dczia/thirtyinone/Hardware/badge/images/build-instructions.pdf

# Hamster’s Build Instructions

## You will need

Wire Cutters
Soldering Iron
Rosin Core Solder

Locate the 5 long socket strips. They look like this:

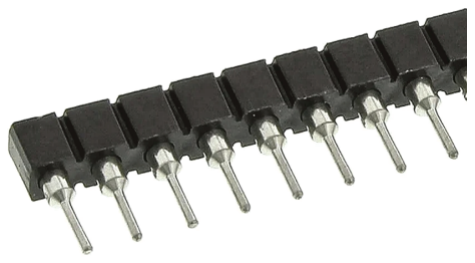
[picture p8: figure]

Using your wire cutters or your fingers, snap off 2-pin

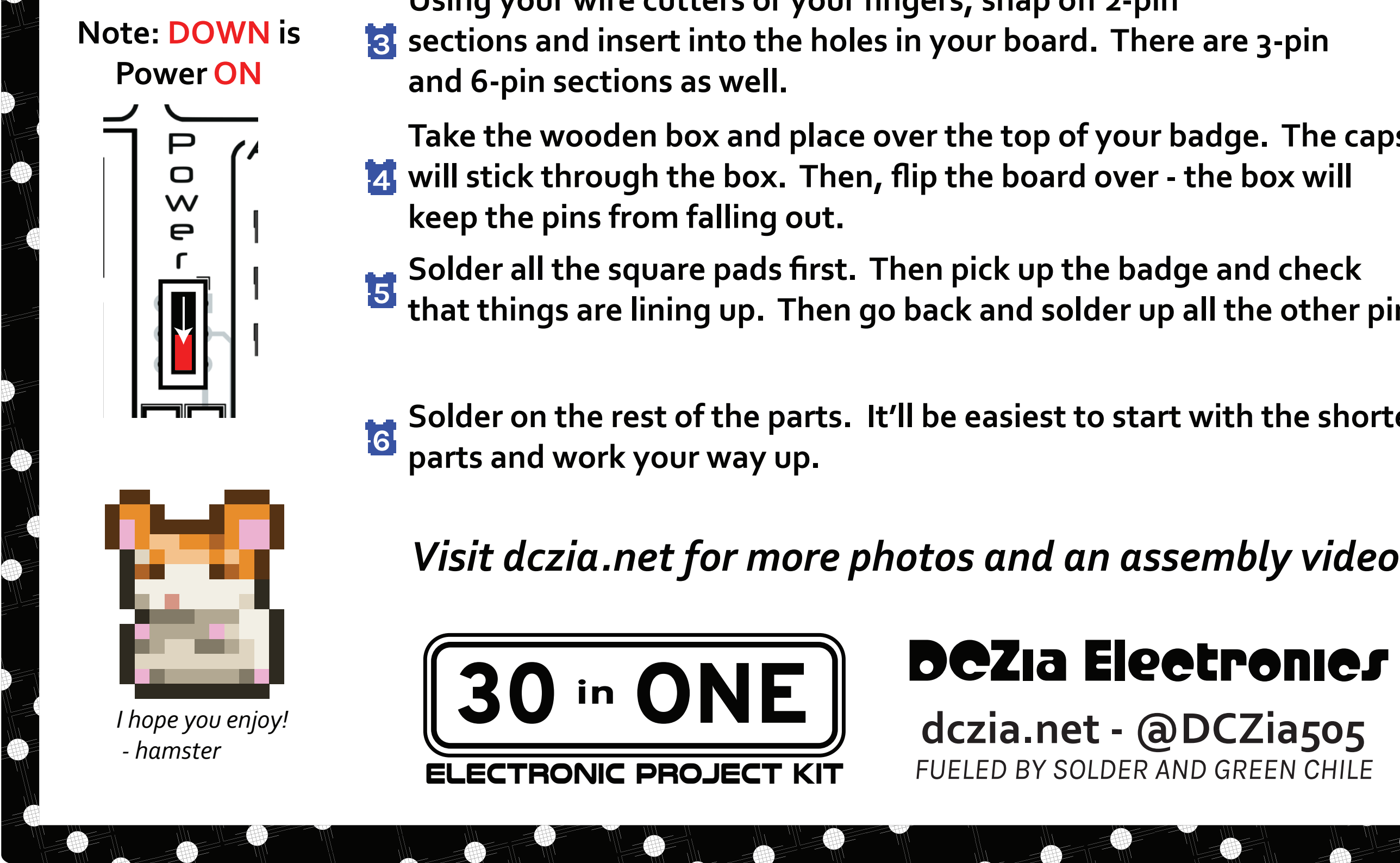
[picture p9: figure]
DCZia Electronics 30; ELECTRONIC PROJECT KIT; in ONE; and 6-pin sections as well.; keep the pins from falling out.; parts and work your way up.; Note: DOWN is Power ON; I hope you enjoy!; - hamster; dczia.net - @DCZia505; FUELED BY SOLDER AND GREEN CHILE

sections and insert into the holes in your board. There are 3-pin

Take the wooden box and place over the top of your badge. The caps will stick through the box. Then, flip the board over - the box will

Solder all the square pads first. Then pick up the badge and check that things are lining up. Then go back and solder up all the other pins.

Solder on the rest of the parts. It’ll be easiest to start with the shortest

Remove the top of the box and pull out your board and place it face up on the table.

## Visit dczia.net for more photos and an assembly video

1

2
