dczia/thirtyinone/Hardware/badge/outputs/thirtyinone-badge.pdf

File: thirtyinone-badge.kicad_sch Sheet: / DCZia

Id: 1/2 Title: 30-in-One


defcon 30
Sheet: /Analog Circuits/ DCZia

File: circuits.kicad_sch
Id: 2/2 Title: 30-in-One
