dczia/thirtyinone/Hardware/circuits/outputs/thirtyinone-circuits.pdf

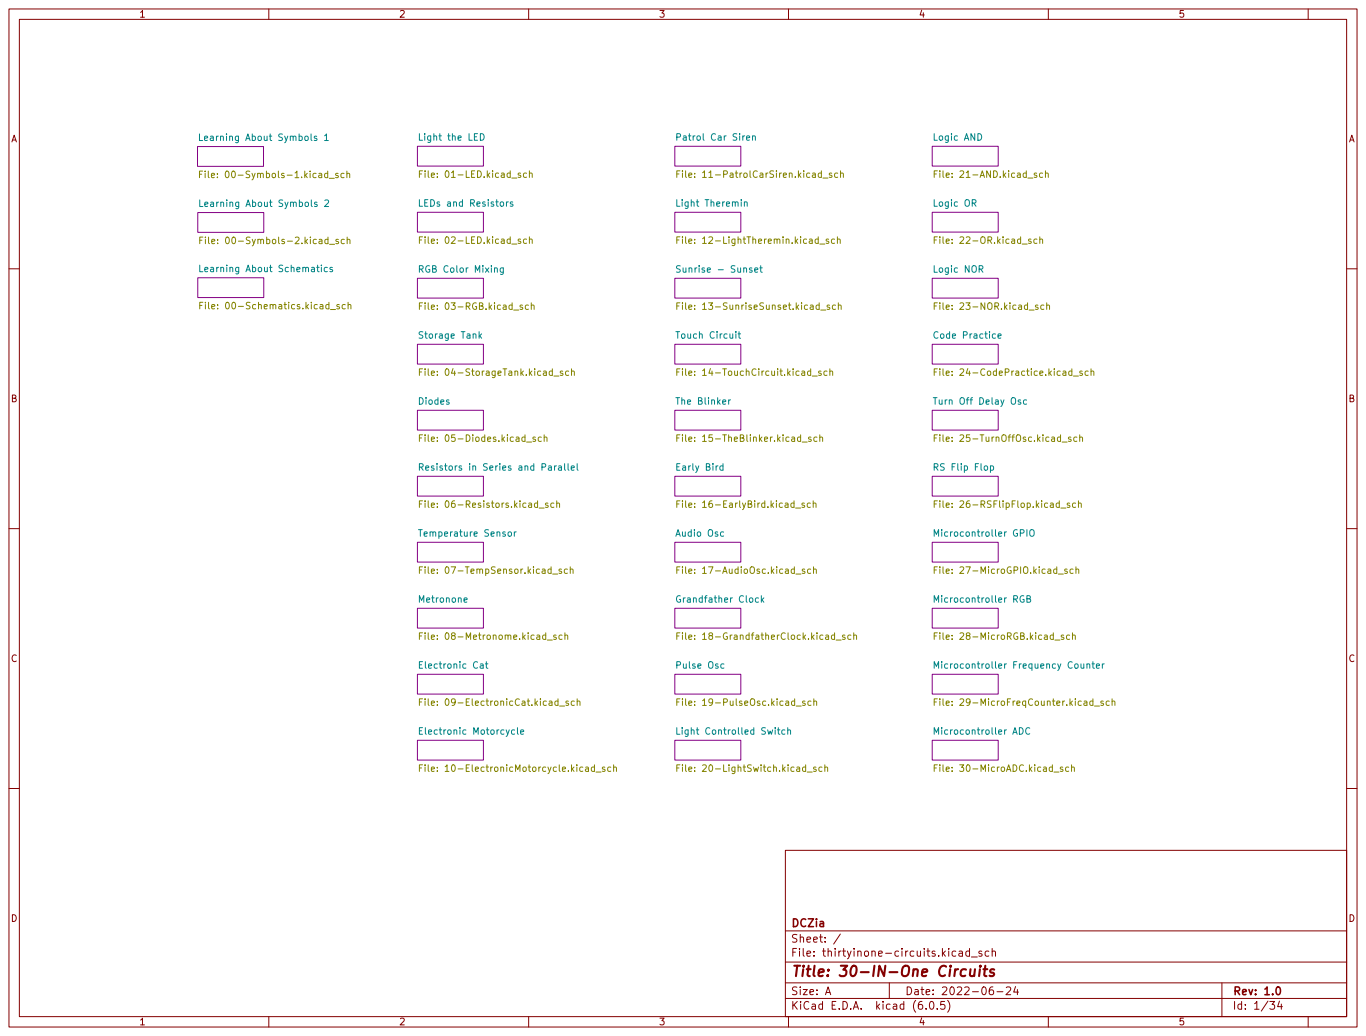
[picture p24: page 1]

File: 16-EarlyBird.kicad_sch Sunrise - Sunset File: 13-SunriseSunset.kicad_sch The Blinker File: 15-TheBlinker.kicad_sch Touch Circuit File: 14-TouchCircuit.kicad_sch Patrol Car Siren File: 11-PatrolCarSiren.kicad_sch
File: 21-AND.kicad_sch Turn Off Delay Osc File: 25-TurnOffOsc.kicad_sch

LEDs and Resistors File: 02-LED.kicad_sch

Learning About Schematics File: 00-Schematics.kicad_sch

Diodes File: 05-Diodes.kicad_sch Temperature Sensor

File: 20-LightSwitch.kicad_sch Grandfather Clock File: 18-GrandfatherClock.kicad_sch Early Bird

File: 26-RSFlipFlop.kicad_sch Microcontroller GPIO

File: 27-MicroGPIO.kicad_sch Microcontroller Frequency Counter

File: 30-MicroADC.kicad_sch Microcontroller RGB

File: 29-MicroFreqCounter.kicad_sch Microcontroller ADC

File: thirtyinone-circuits.kicad_sch Sheet: / DCZia

Id: 1/34 Title: 30-IN-One Circuits

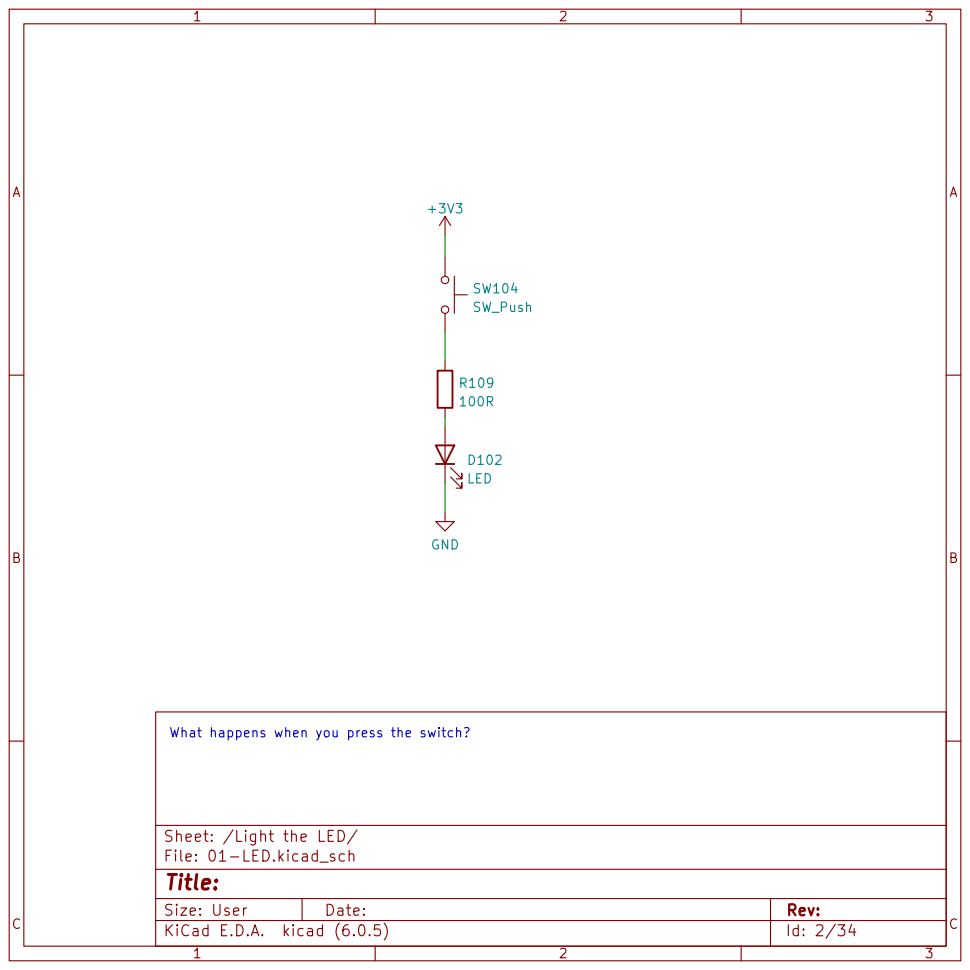
[picture p25: page 2]

LED GND What happens when you press the switch?

Sheet: /Light the LED/
File: 01-LED.kicad_sch
Id: 2/34 Title:

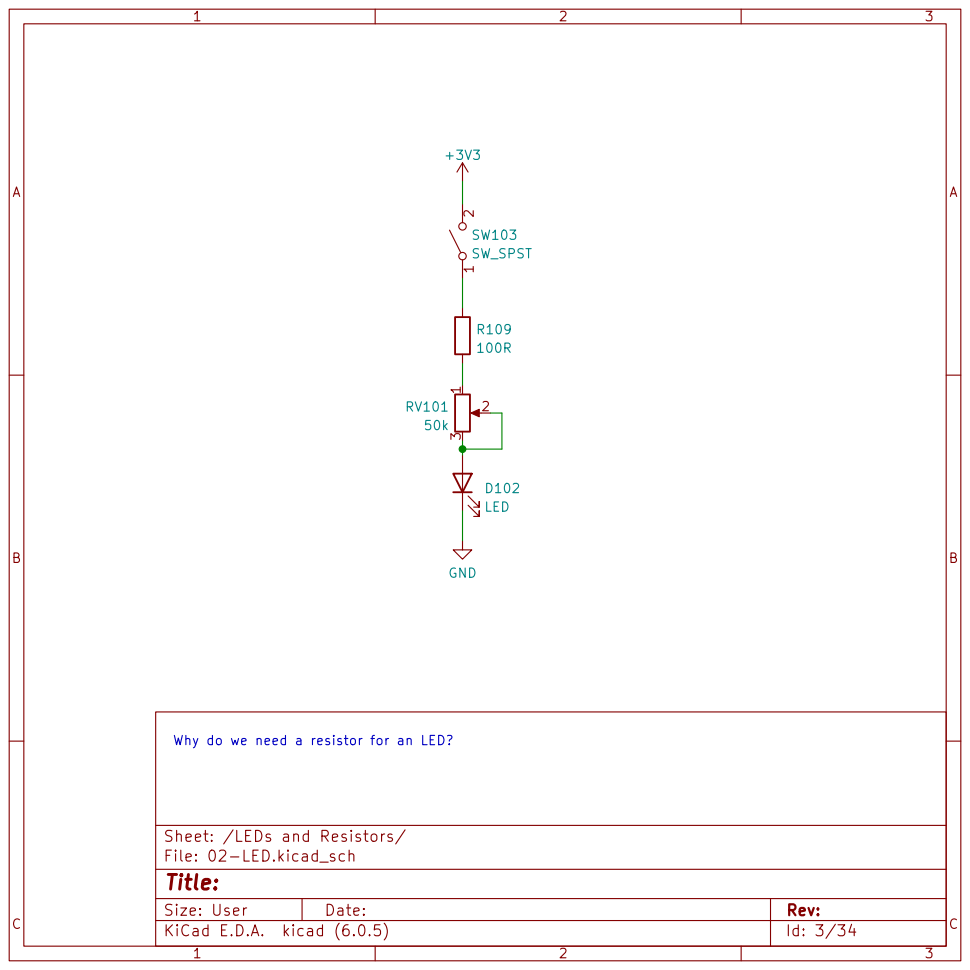
[picture p26: page 3]

1 2 SW103 SW_SPST Why do we need a resistor for an LED?

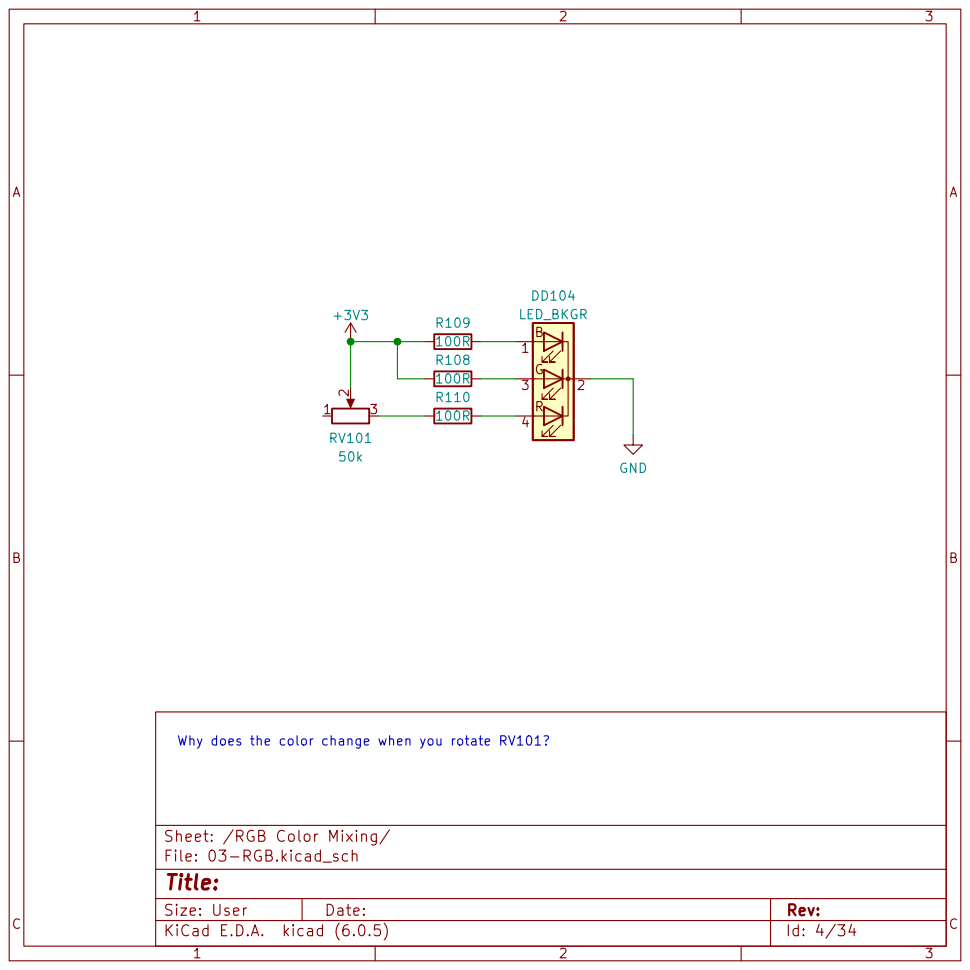
[picture p27: page 4]

50k Why does the color change when you rotate RV101?

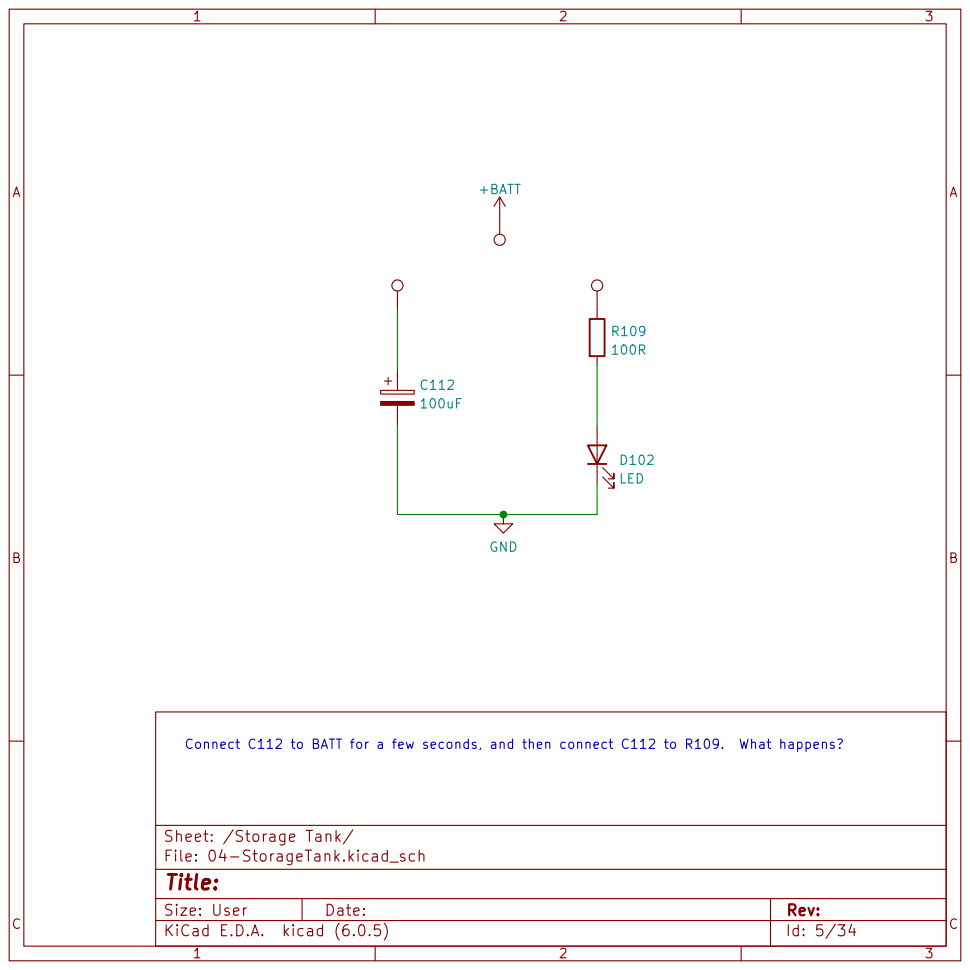
[picture p28: page 5]

+BATT Connect C112 to BATT for a few seconds, and then connect C112 to R109. What happens?

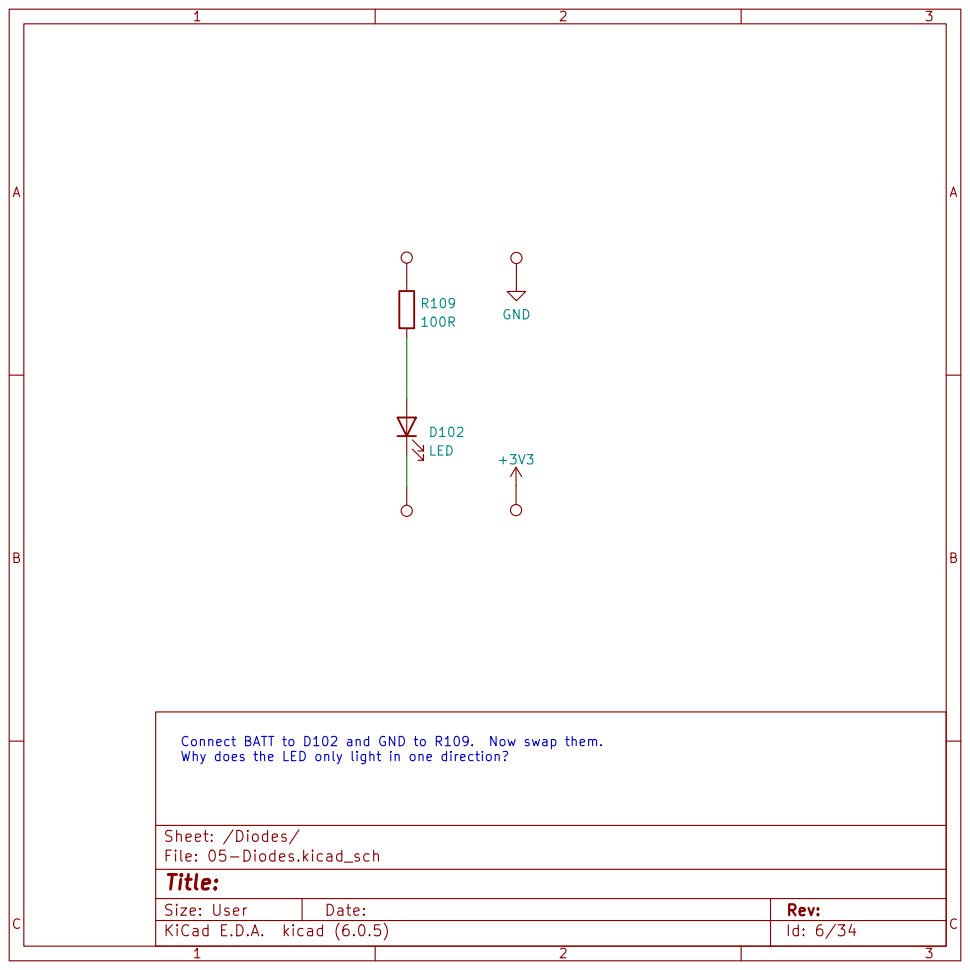
[picture p29: page 6]

+3V3 Connect BATT to D102 and GND to R109. Now swap them.

Why does the LED only light in one direction?

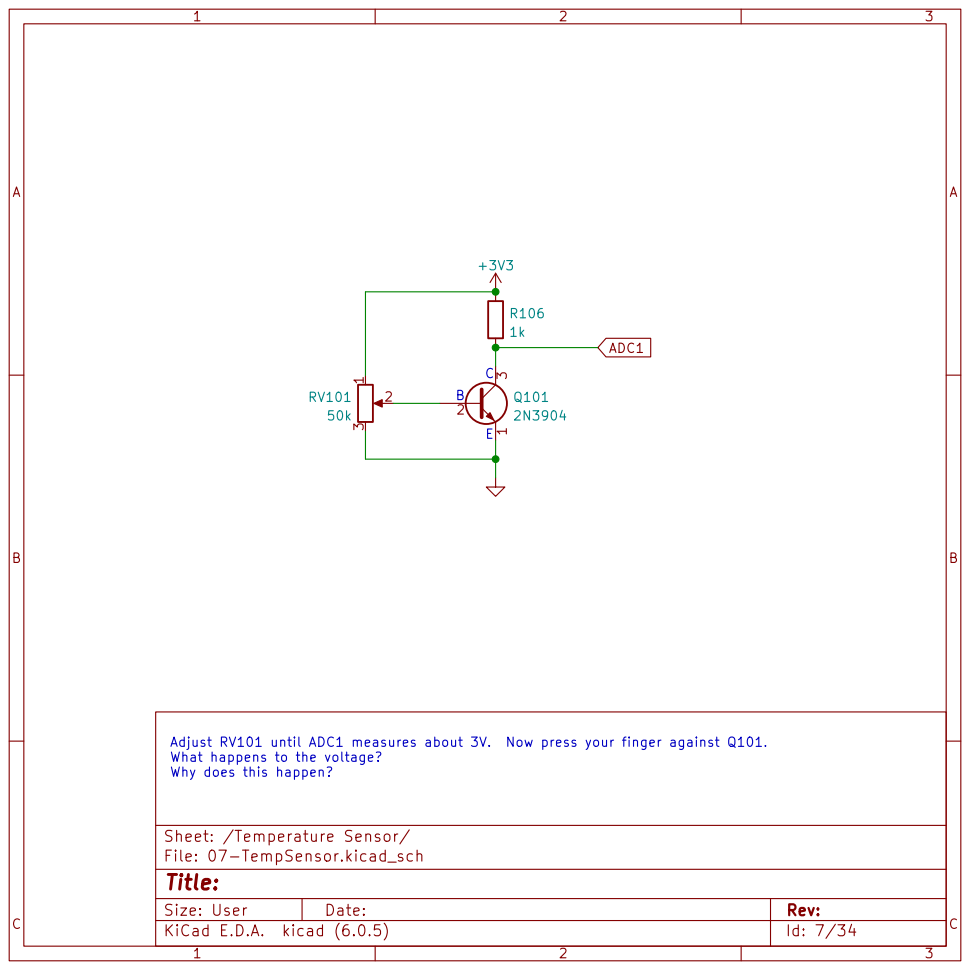
[picture p30: page 7]

Adjust RV101 until ADC1 measures about 3V. Now press your finger against Q101.
What happens to the voltage?
Why does this happen?

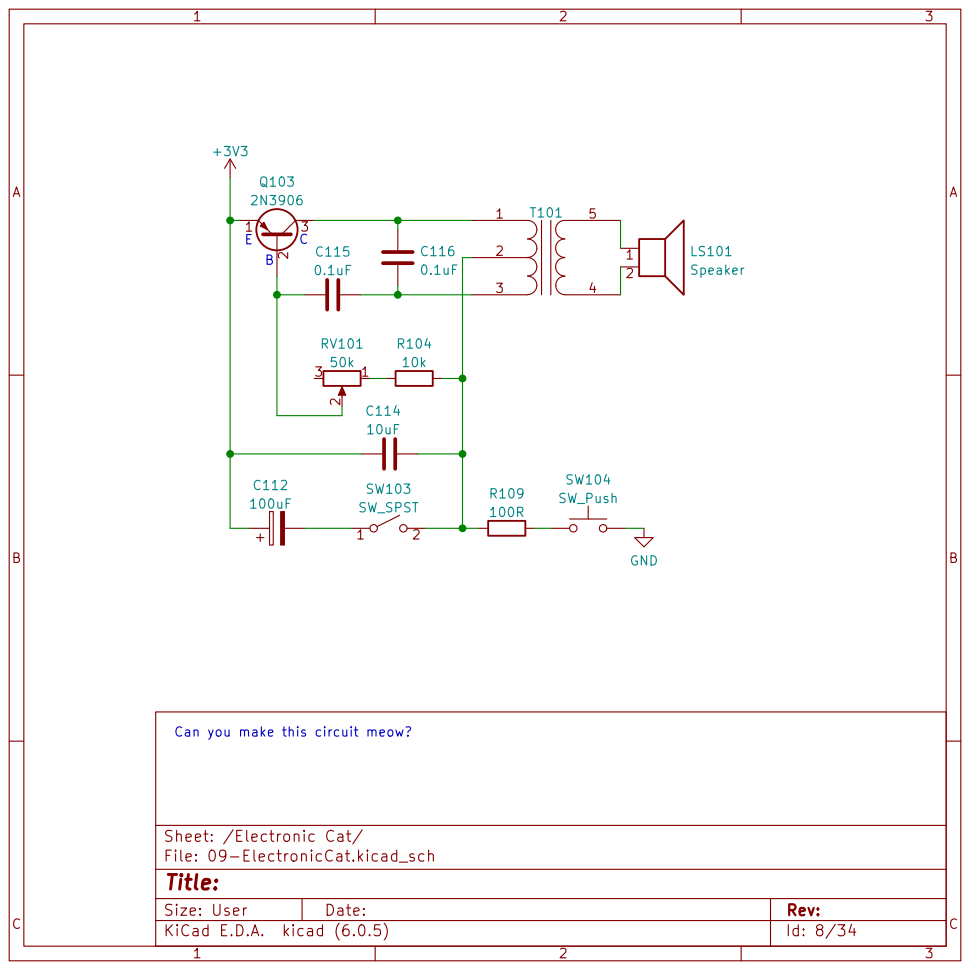
[picture p31: page 8]

Can you make this circuit meow? B

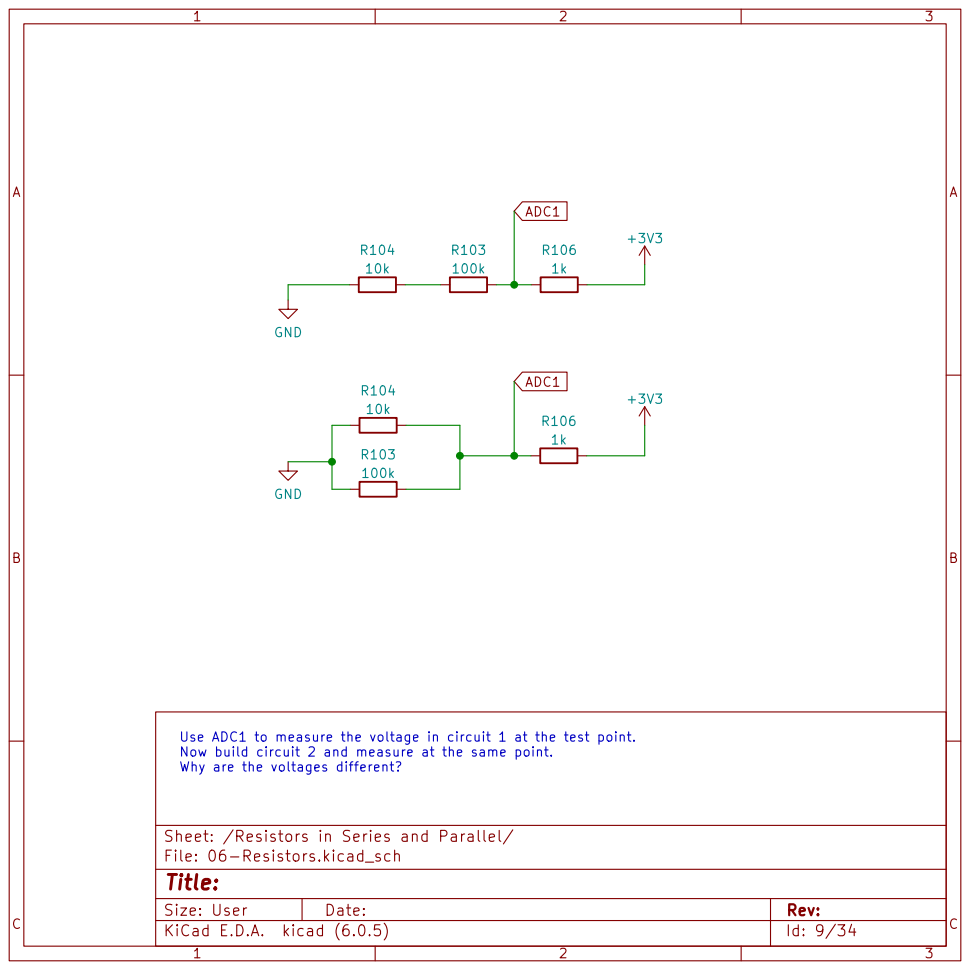
[picture p32: page 9]

Now build circuit 2 and measure at the same point.
Why are the voltages different?

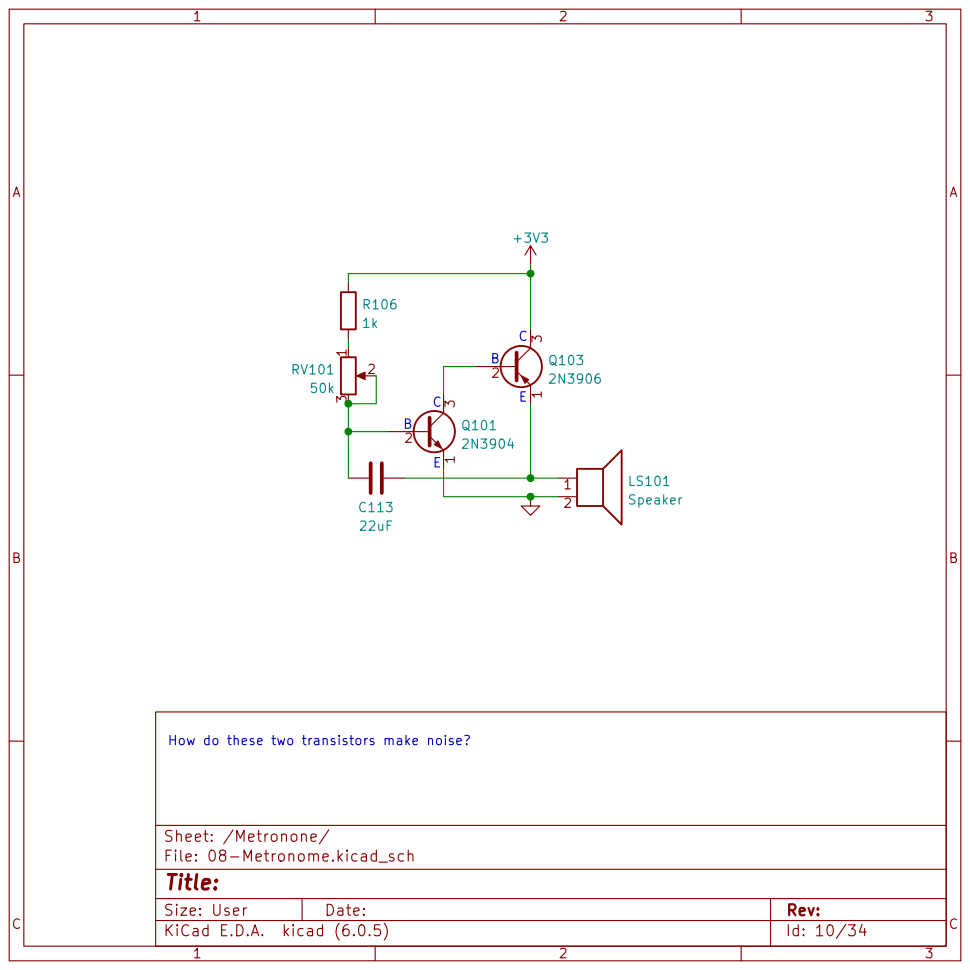
[picture p33: page 10]

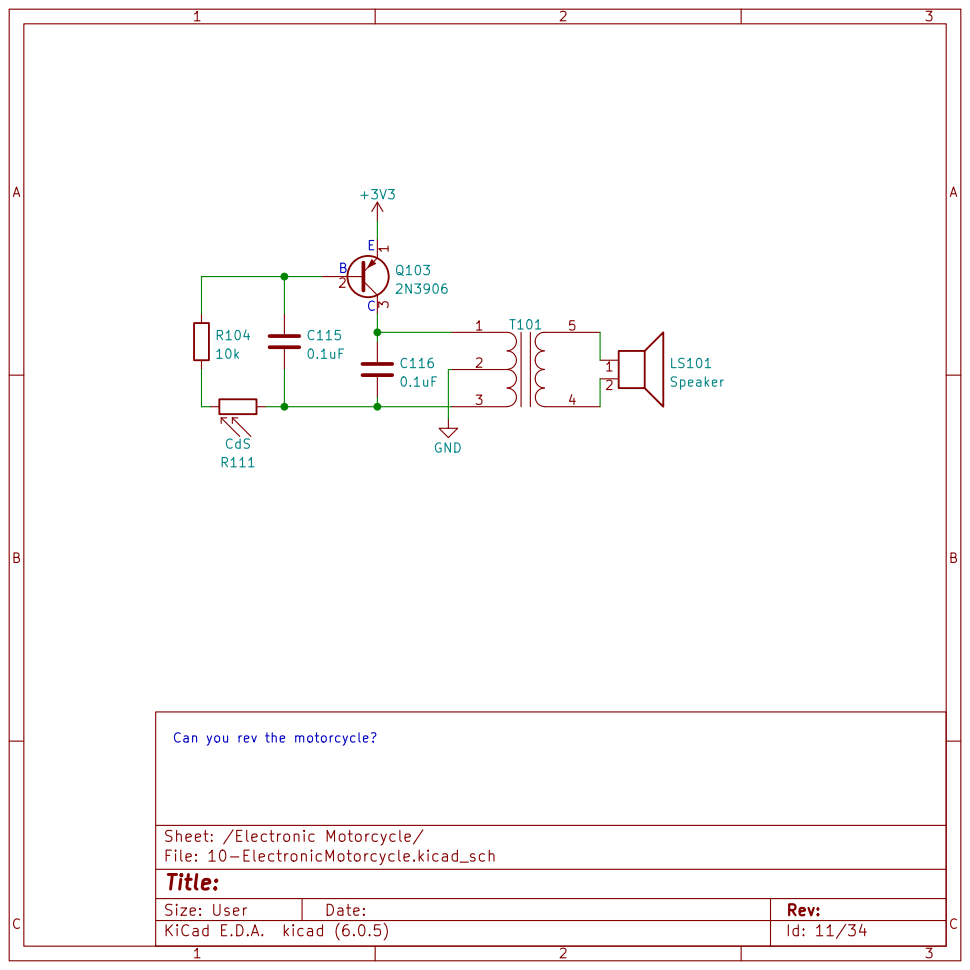
[picture p34: page 11]

Can you rev the motorcycle?

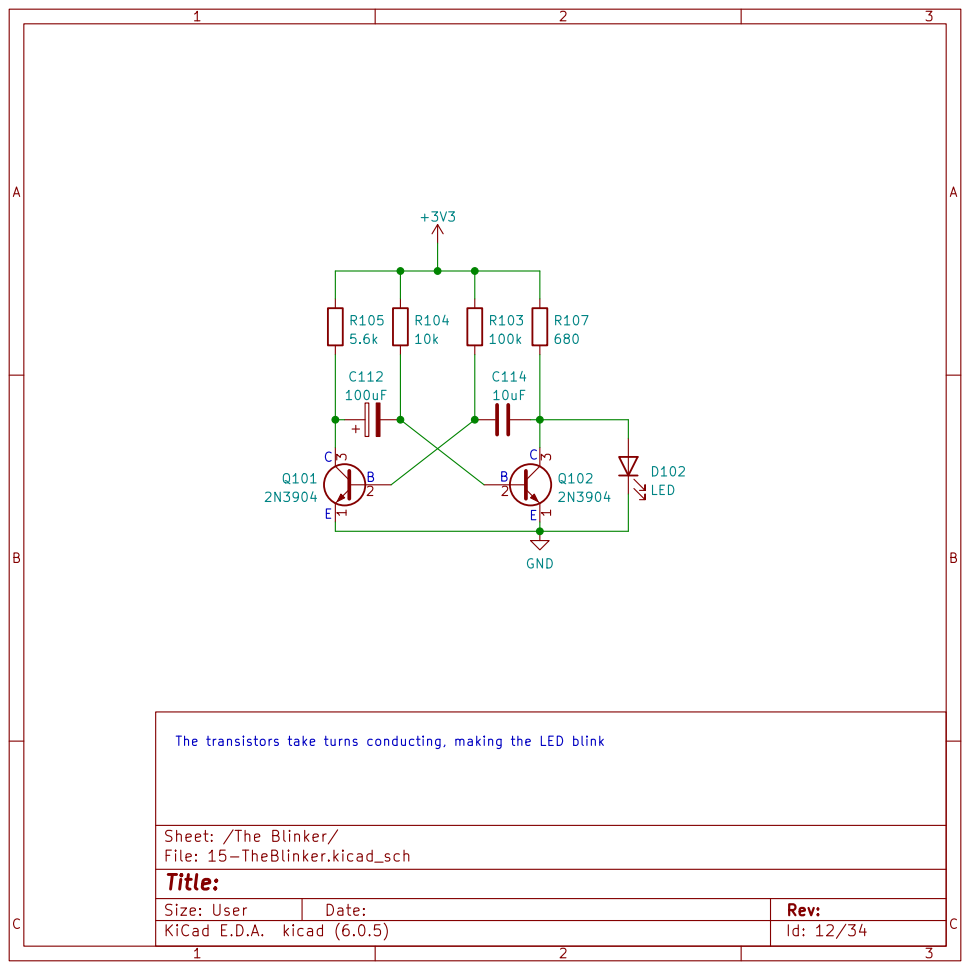
[picture p35: page 12]

The transistors take turns conducting, making the LED blink E

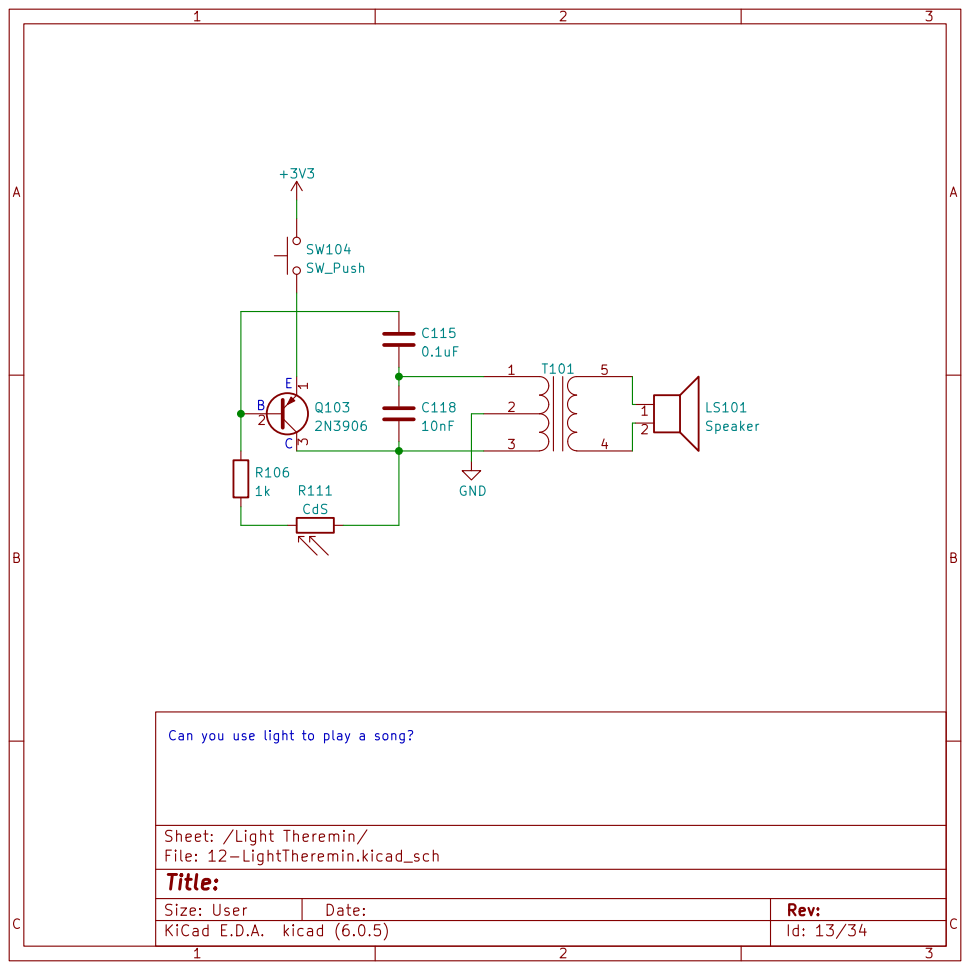
[picture p36: page 13]

Can you use light to play a song?

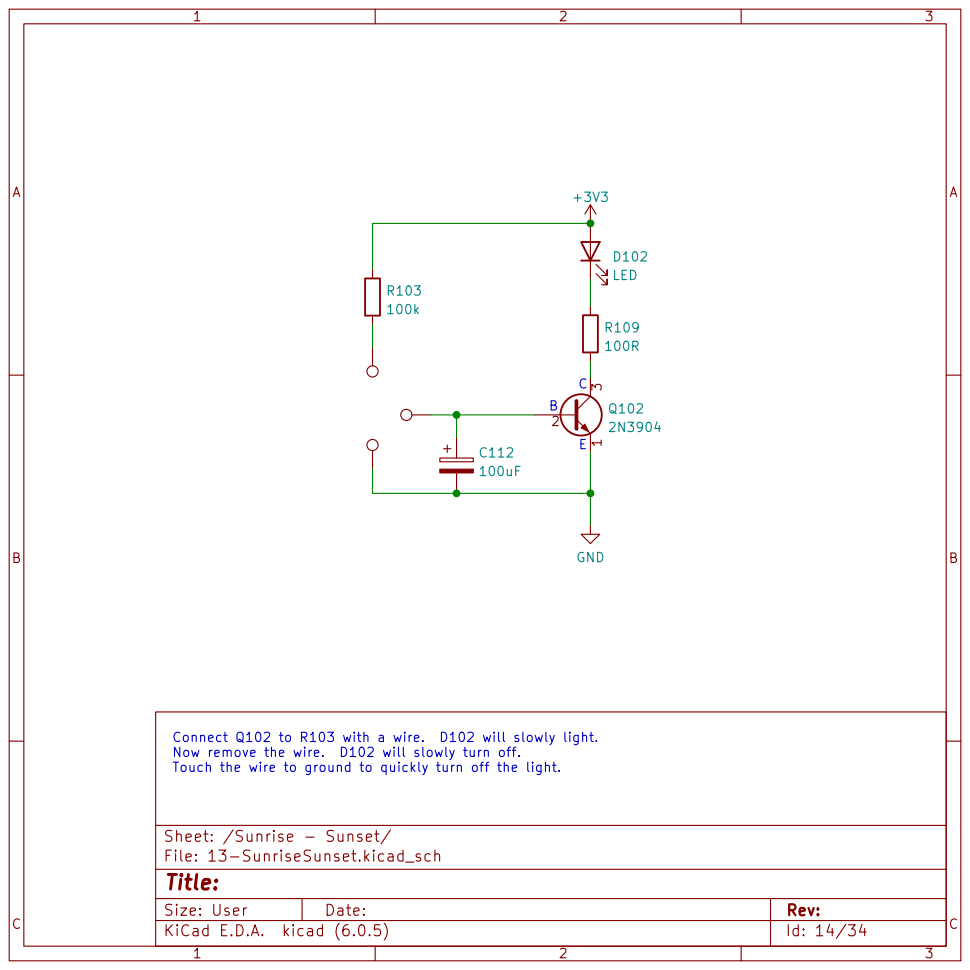
[picture p37: page 14]

Connect Q102 to R103 with a wire. D102 will slowly light.
Now remove the wire. D102 will slowly turn off.
Touch the wire to ground to quickly turn off the light.

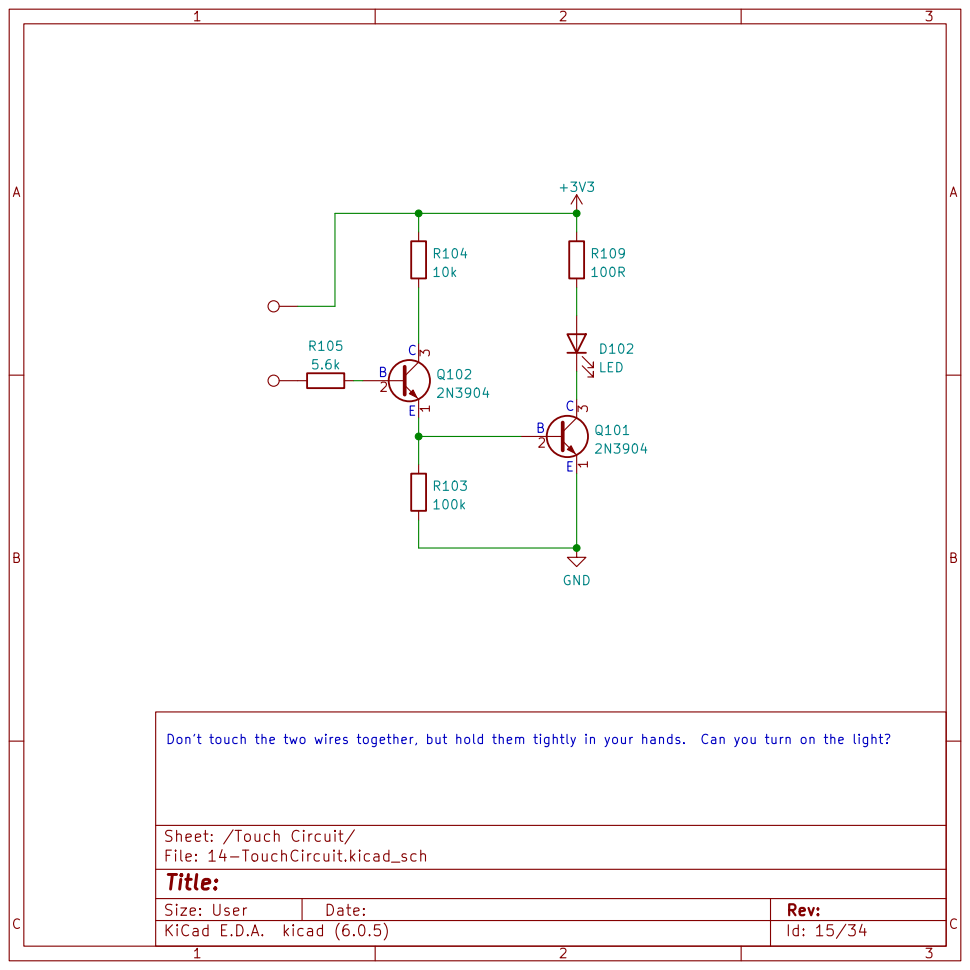
[picture p38: page 15]

B Don't touch the two wires together, but hold them tightly in your hands. Can you turn on the light? C E

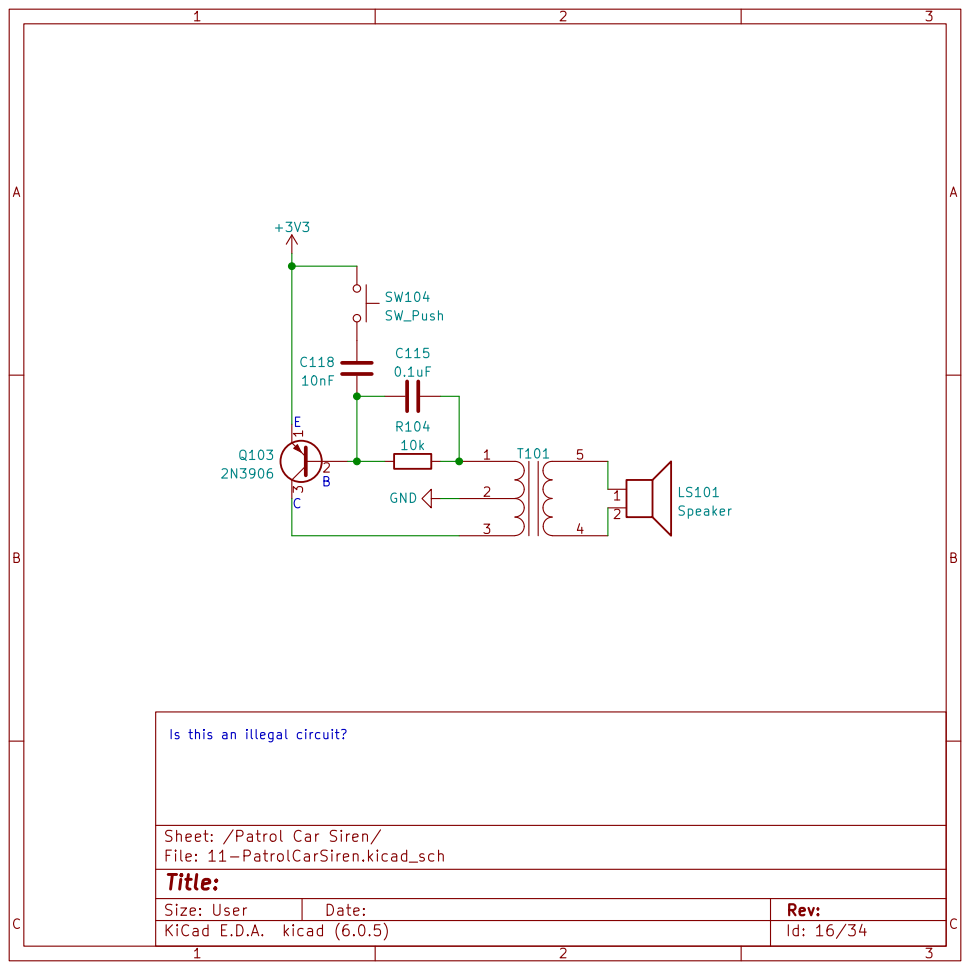
[picture p39: page 16]

File: 11-PatrolCarSiren.kicad_sch Sheet: /Patrol Car Siren/ C118

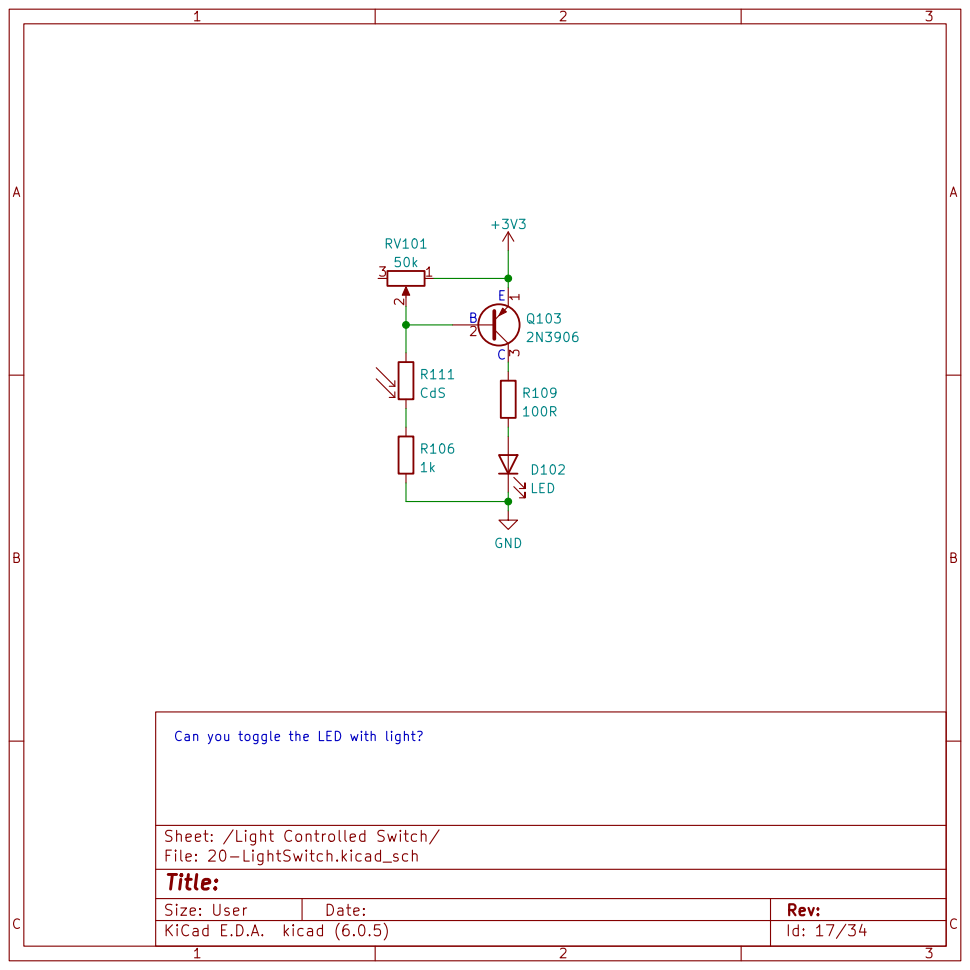
[picture p40: page 17]

Can you toggle the LED with light?

Sheet: /Light Controlled Switch/
File: 20-LightSwitch.kicad_sch
Id: 17/34 Title:

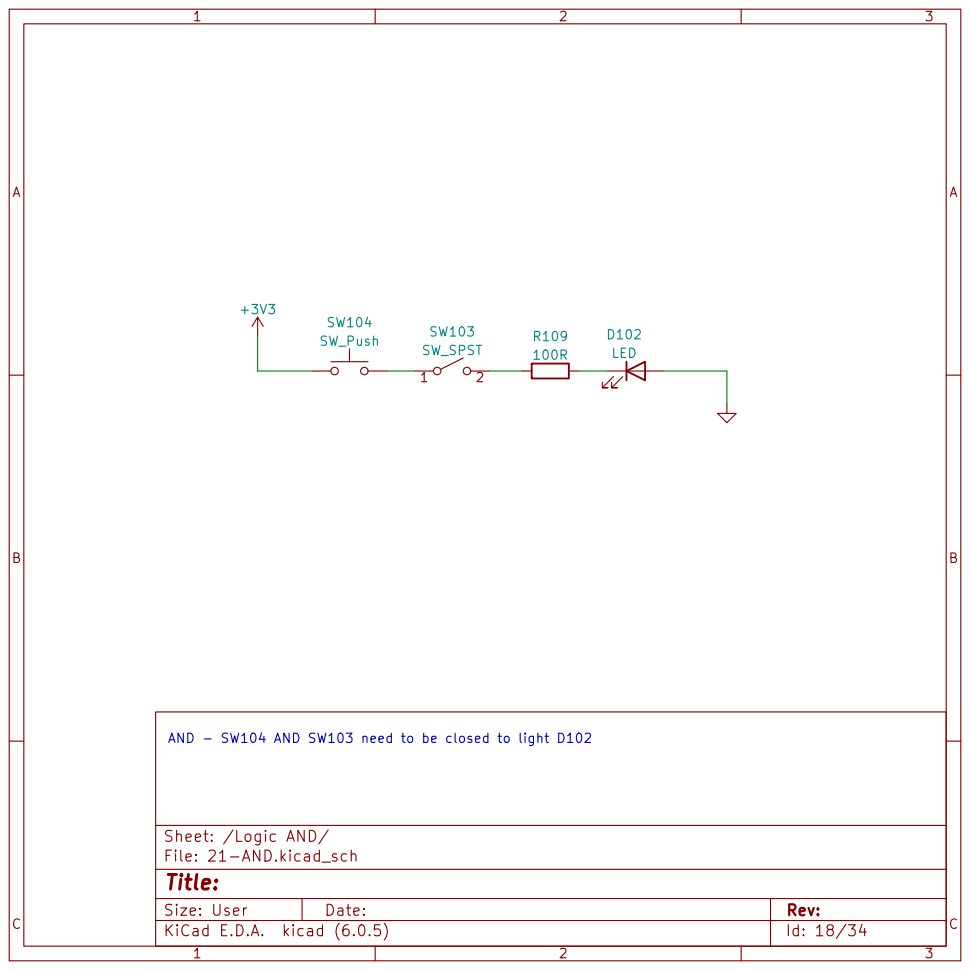
[picture p41: page 18]

AND - SW104 AND SW103 need to be closed to light D102

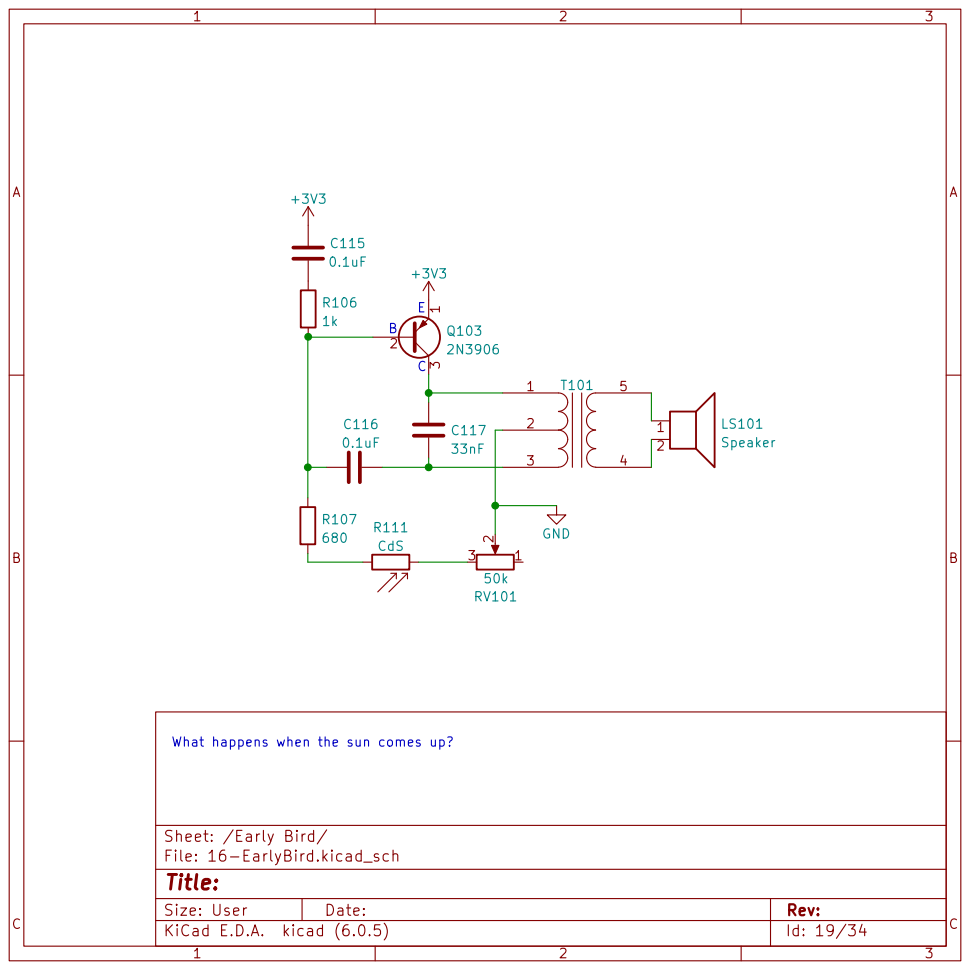
[picture p42: page 19]

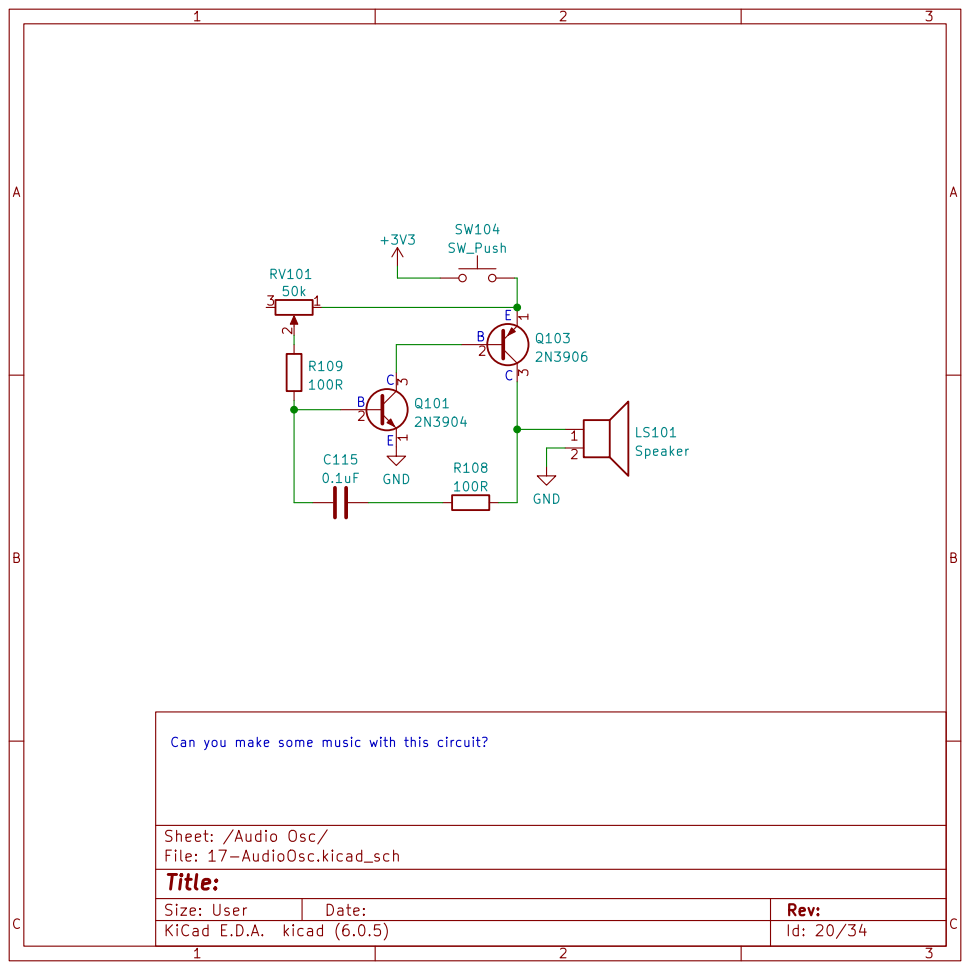
[picture p43: page 20]

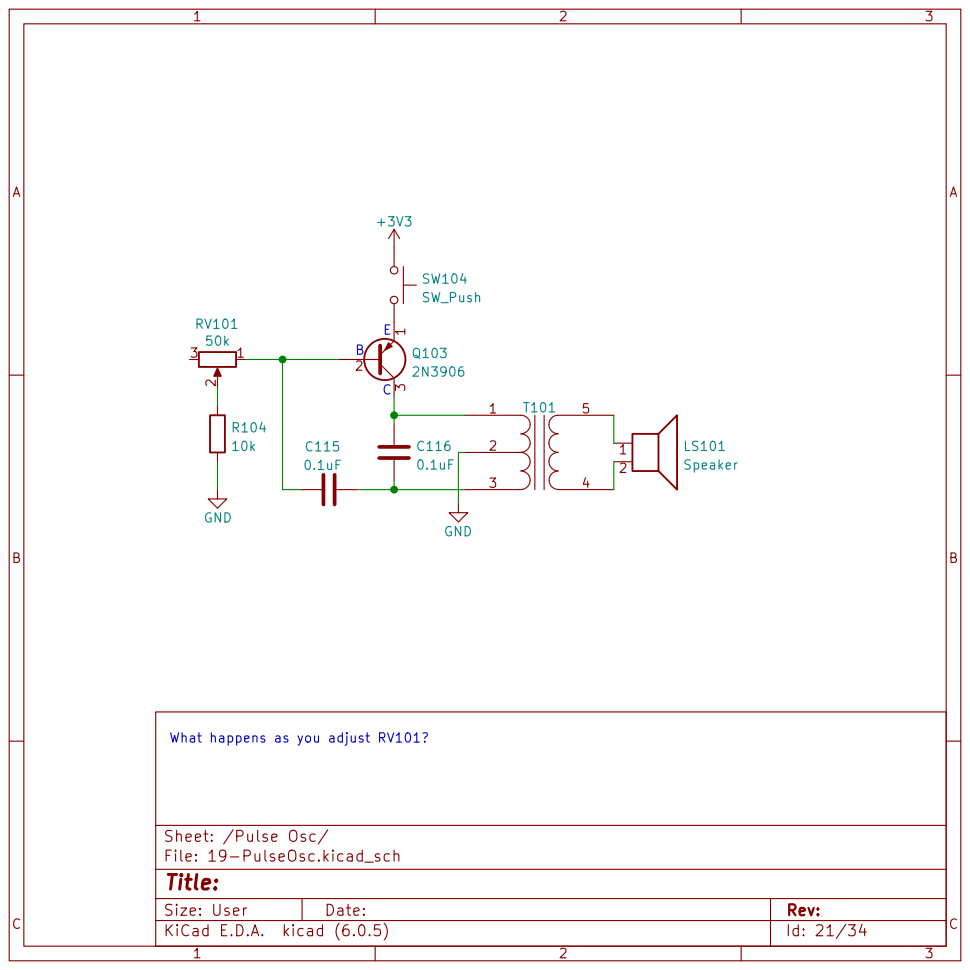
[picture p44: page 21]

File: 19-PulseOsc.kicad_sch Sheet: /Pulse Osc/ 1

0.1uF What happens as you adjust RV101?C

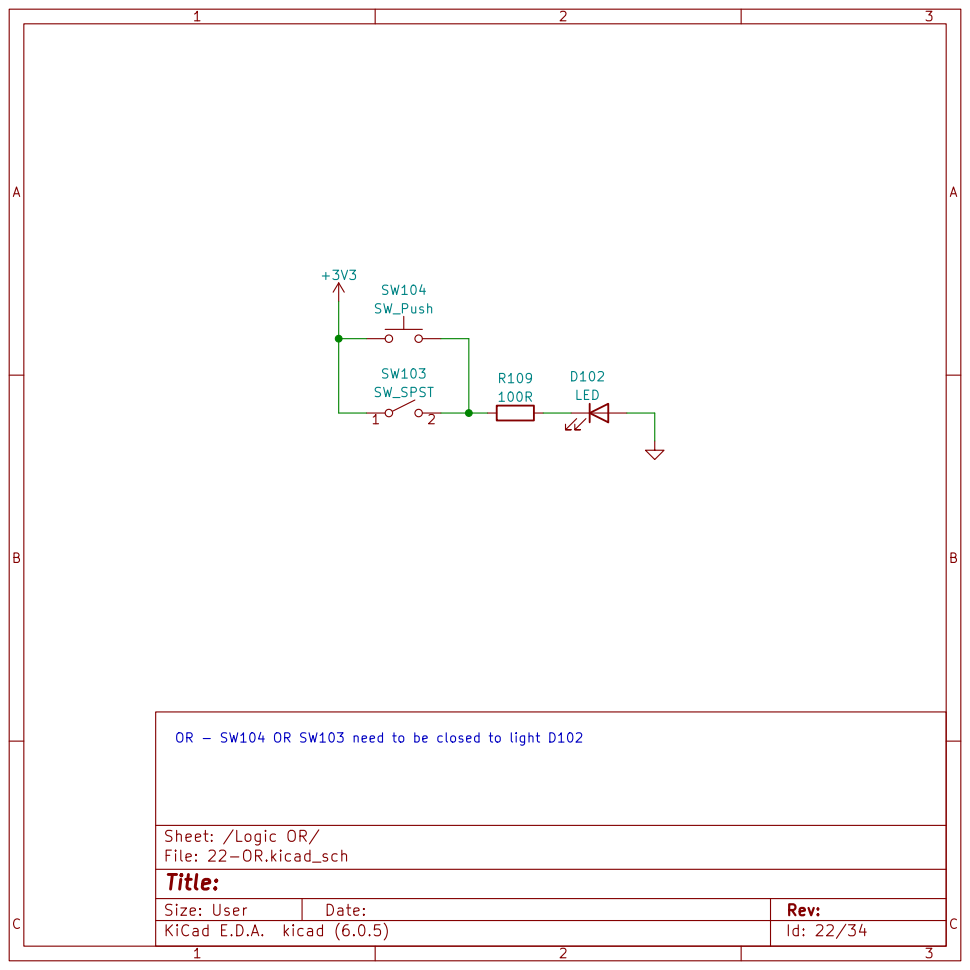
[picture p45: page 22]

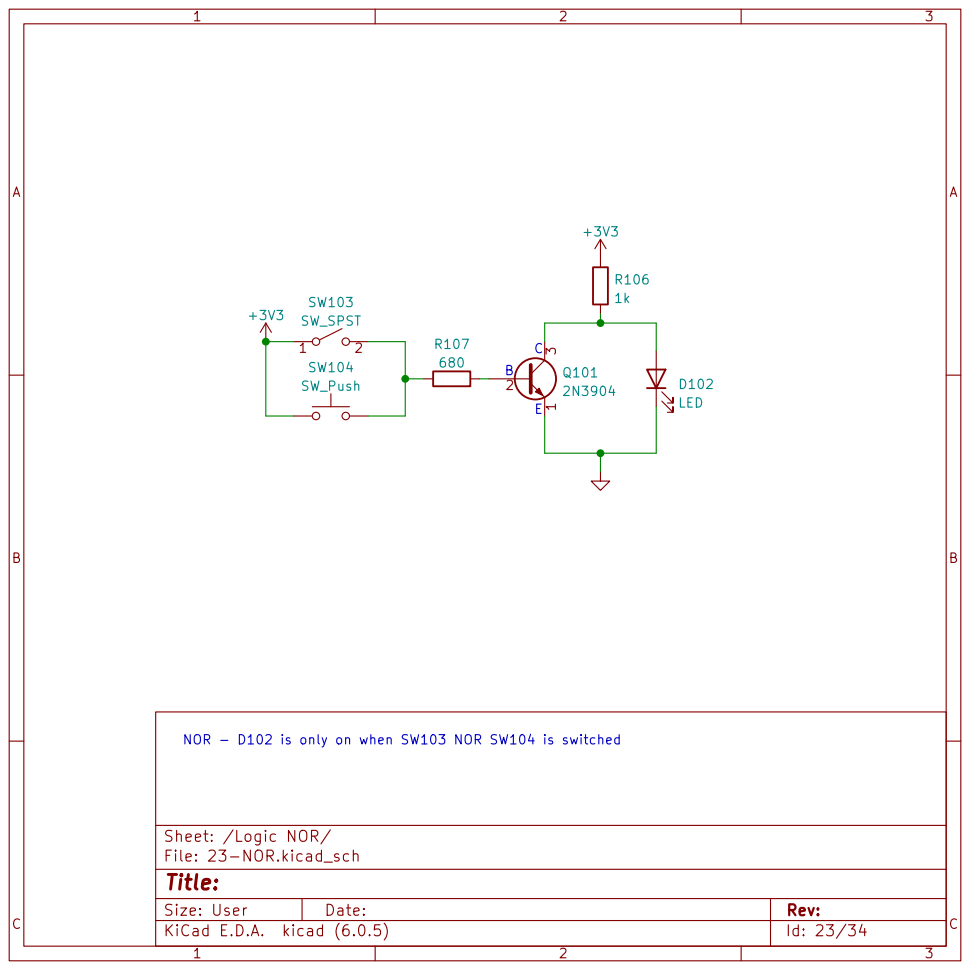
[picture p46: page 23]

B NOR - D102 is only on when SW103 NOR SW104 is switched

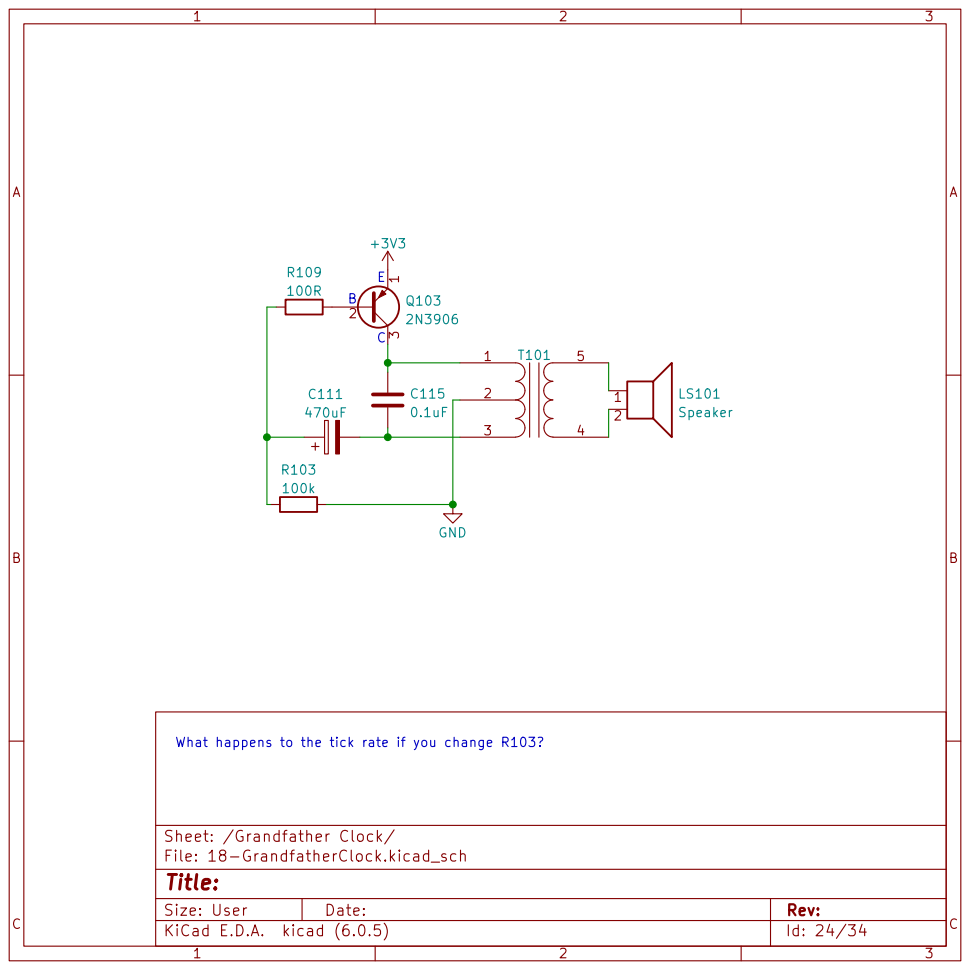
[picture p47: page 24]

File: 18-GrandfatherClock.kicad_sch Sheet: /Grandfather Clock/ R109

2N3906 +3V3 B What happens to the tick rate if you change R103? EC

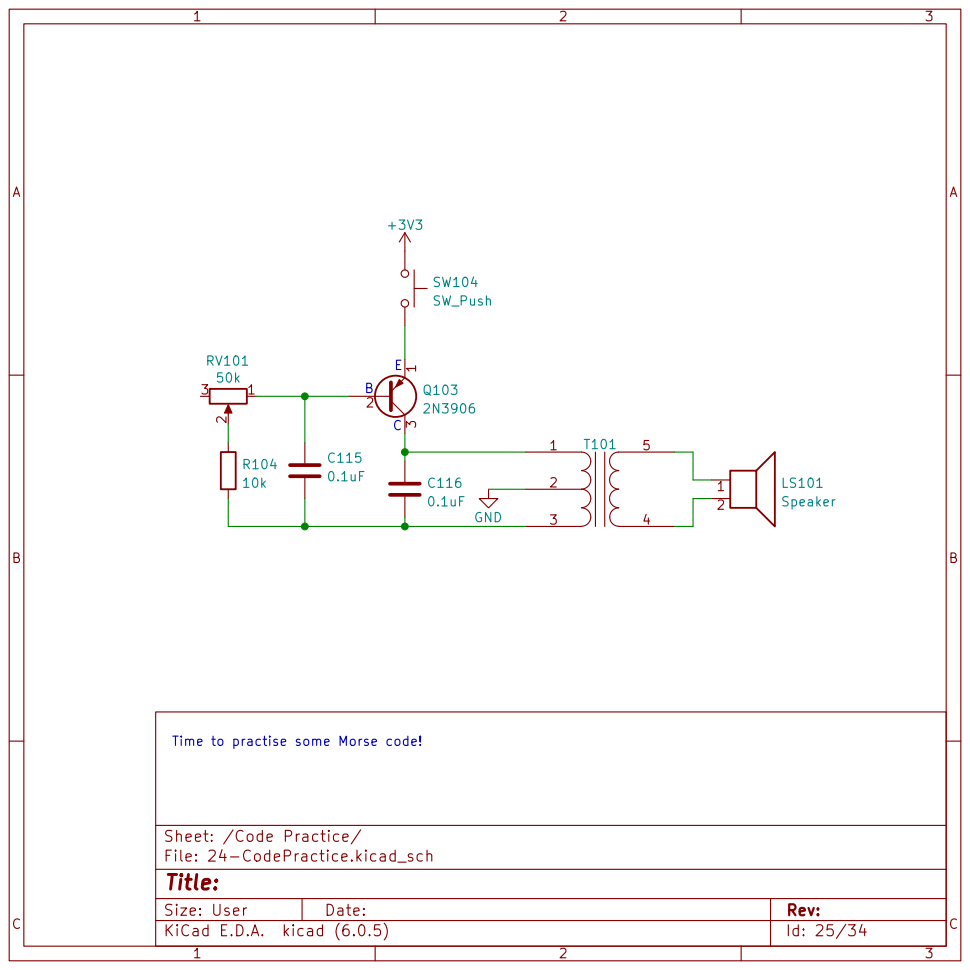
[picture p48: page 25]

File: 24-CodePractice.kicad_sch Sheet: /Code Practice/ R104

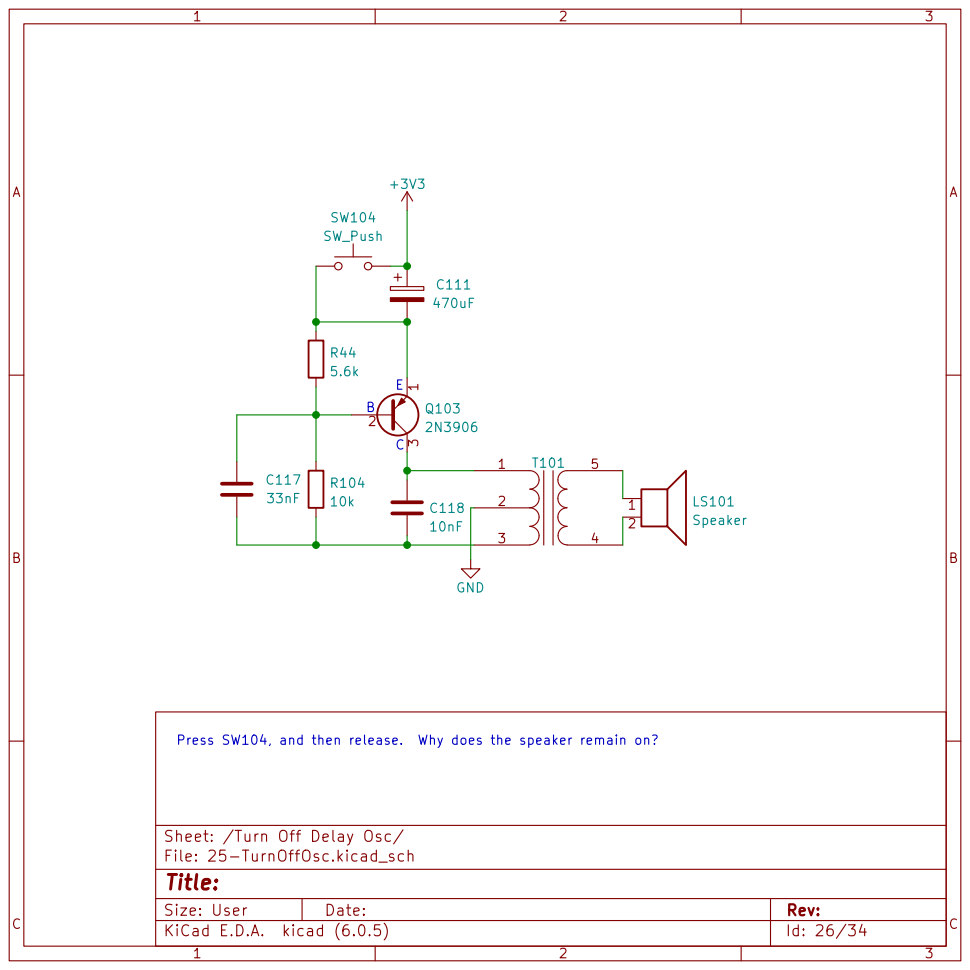
[picture p49: page 26]

Press SW104, and then release. Why does the speaker remain on? C

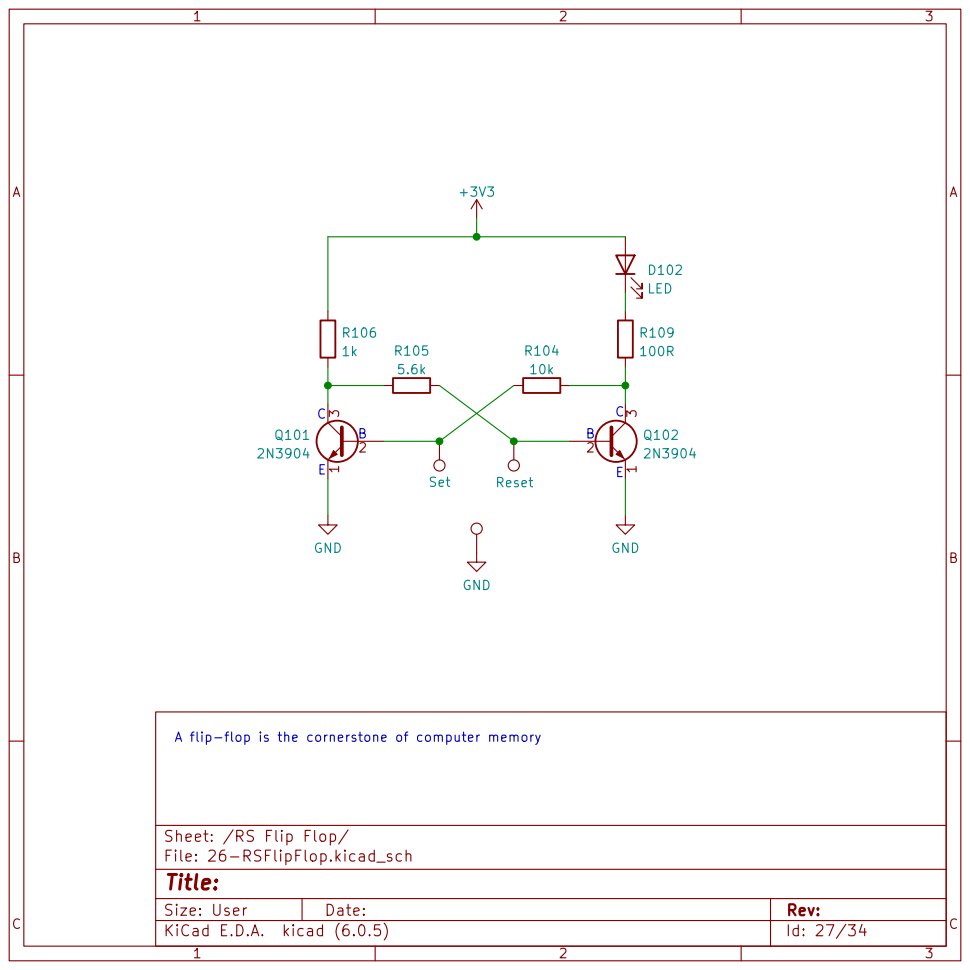
[picture p50: page 27]

A flip-flop is the cornerstone of computer memory

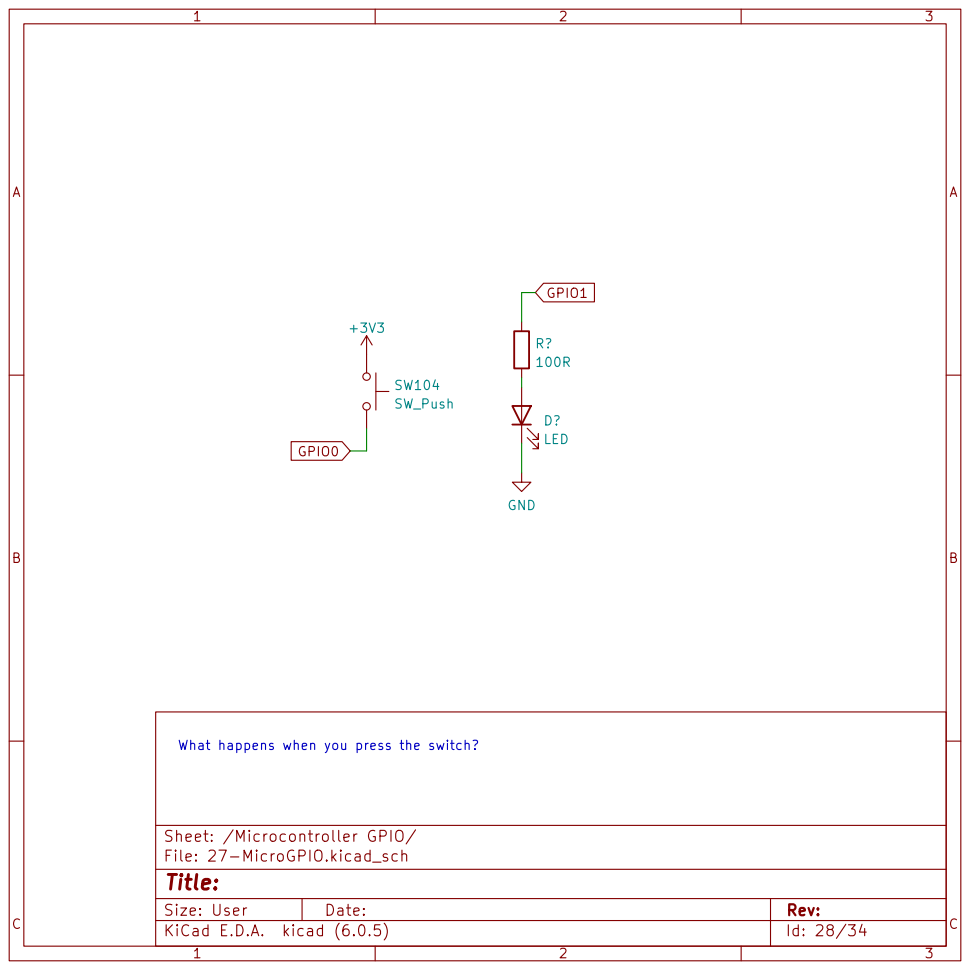
[picture p51: page 28]

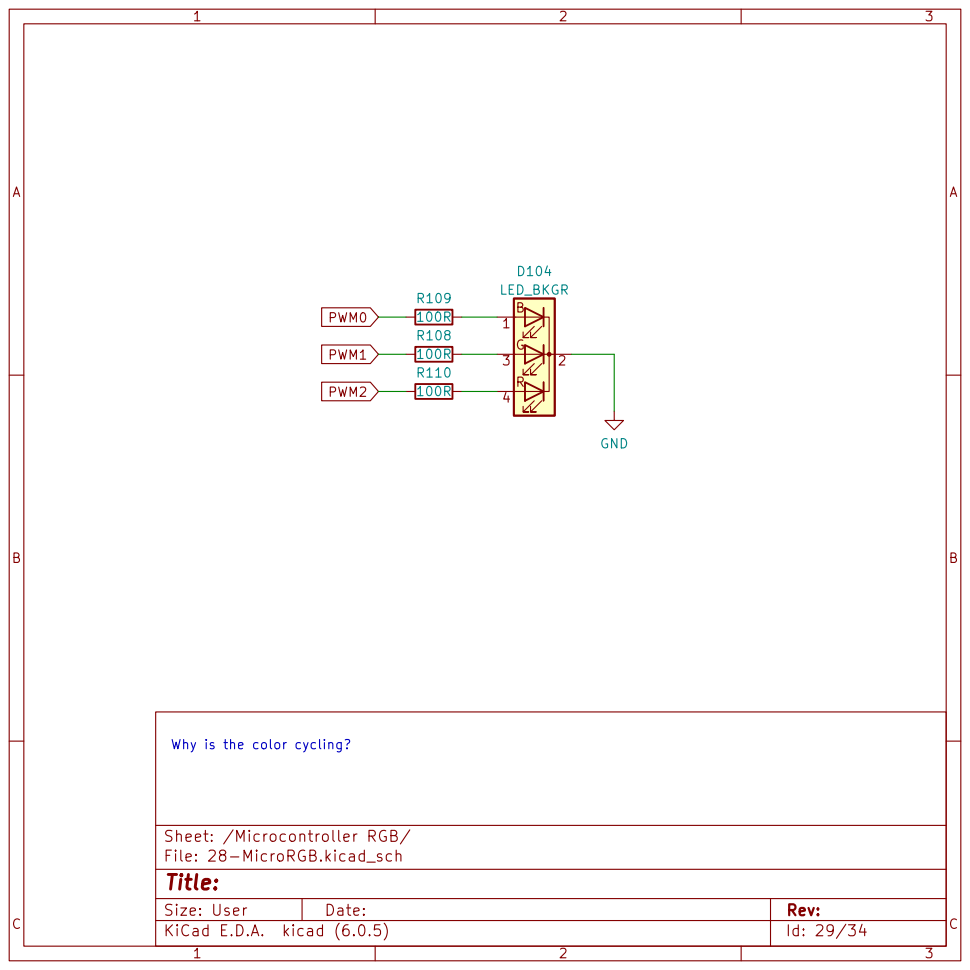
[picture p52: page 29]

PWM2 PWM0 PWM1 Why is the color cycling?

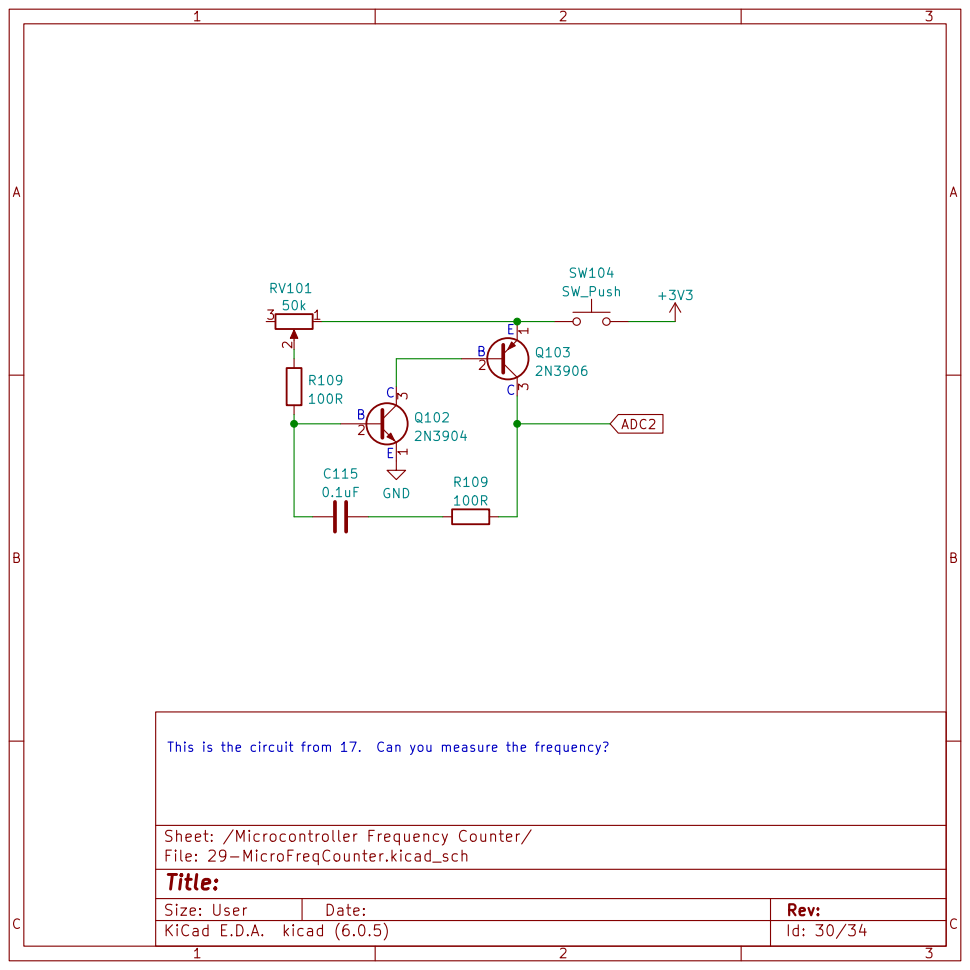
[picture p53: page 30]

This is the circuit from 17. Can you measure the frequency? B

Sheet: /Microcontroller Frequency Counter/ C115

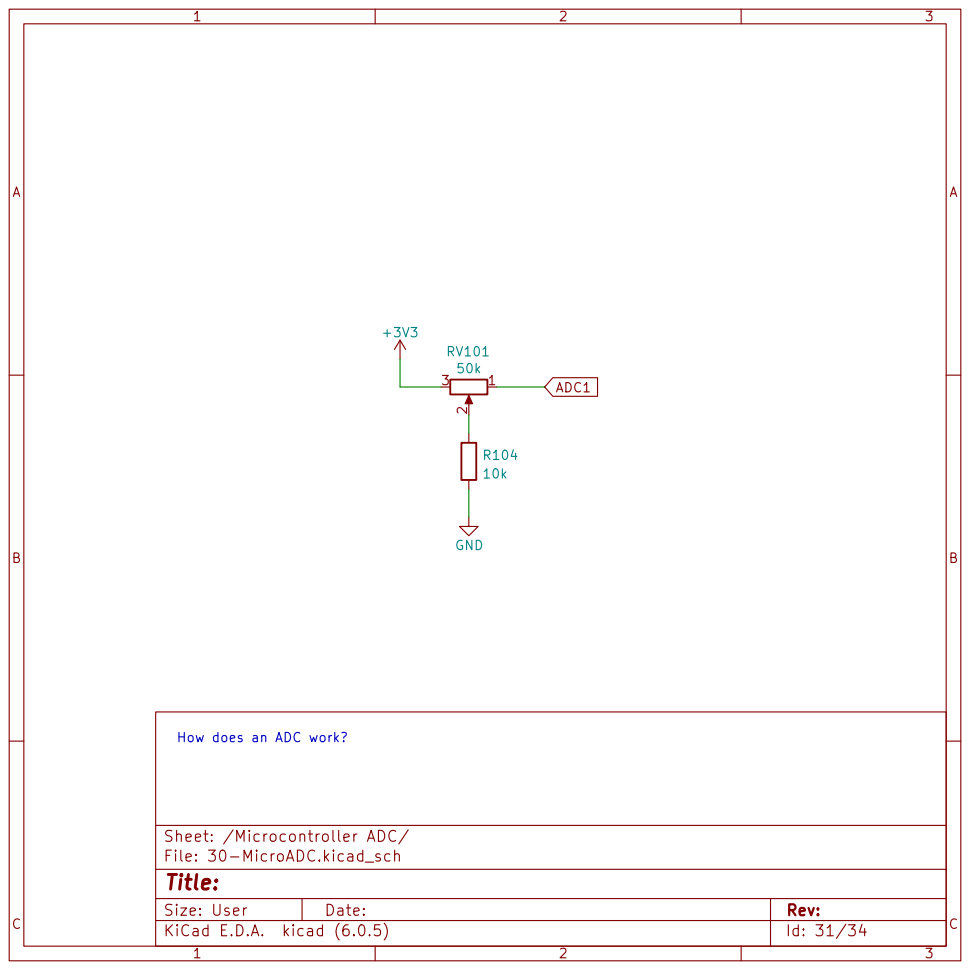
[picture p54: page 31]

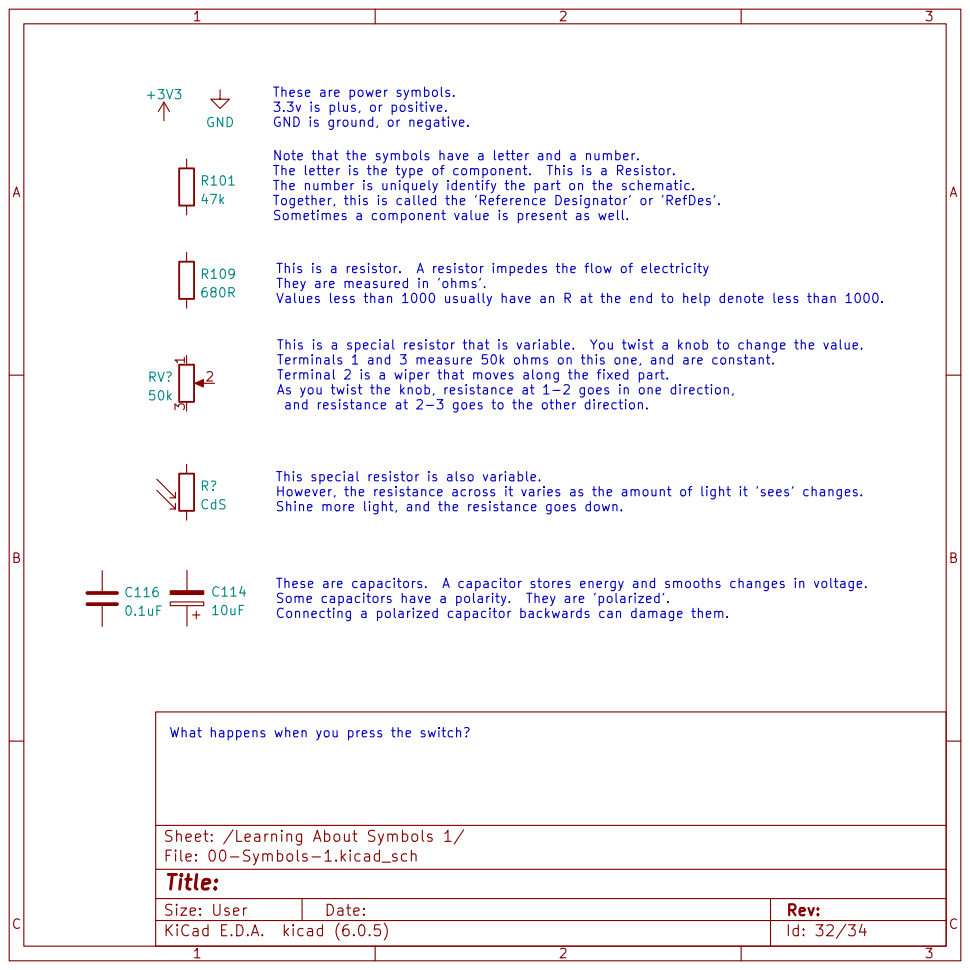
[picture p55: page 32]

These are power symbols.
3.3v is plus, or positive.
GND is ground, or negative.

Note that the symbols have a letter and a number.
The letter is the type of component. This is a Resistor.
The number is uniquely identify the part on the schematic.

Together, this is called the 'Reference Designator' or 'RefDes'.
Sometimes a component value is present as well.

This is a resistor. A resistor impedes the flow of electricity
They are measured in 'ohms'.
Values less than 1000 usually have an R at the end to help denote less than 1000.

This is a special resistor that is variable. You twist a knob to change the value. Terminals 1 and 3 measure 50k ohms on this one, and are constant. Terminal 2 is a wiper that moves along the fixed part.

As you twist the knob, resistance at 1-2 goes in one direction,
and resistance at 2-3 goes to the other direction.

This special resistor is also variable.
However, the resistance across it varies as the amount of light it 'sees' changes.
Shine more light, and the resistance goes down.

Sheet: /Learning About Symbols 1/ C114

Some capacitors have a polarity. They are 'polarized'.
Connecting a polarized capacitor backwards can damage them.

What happens when you press the switch?

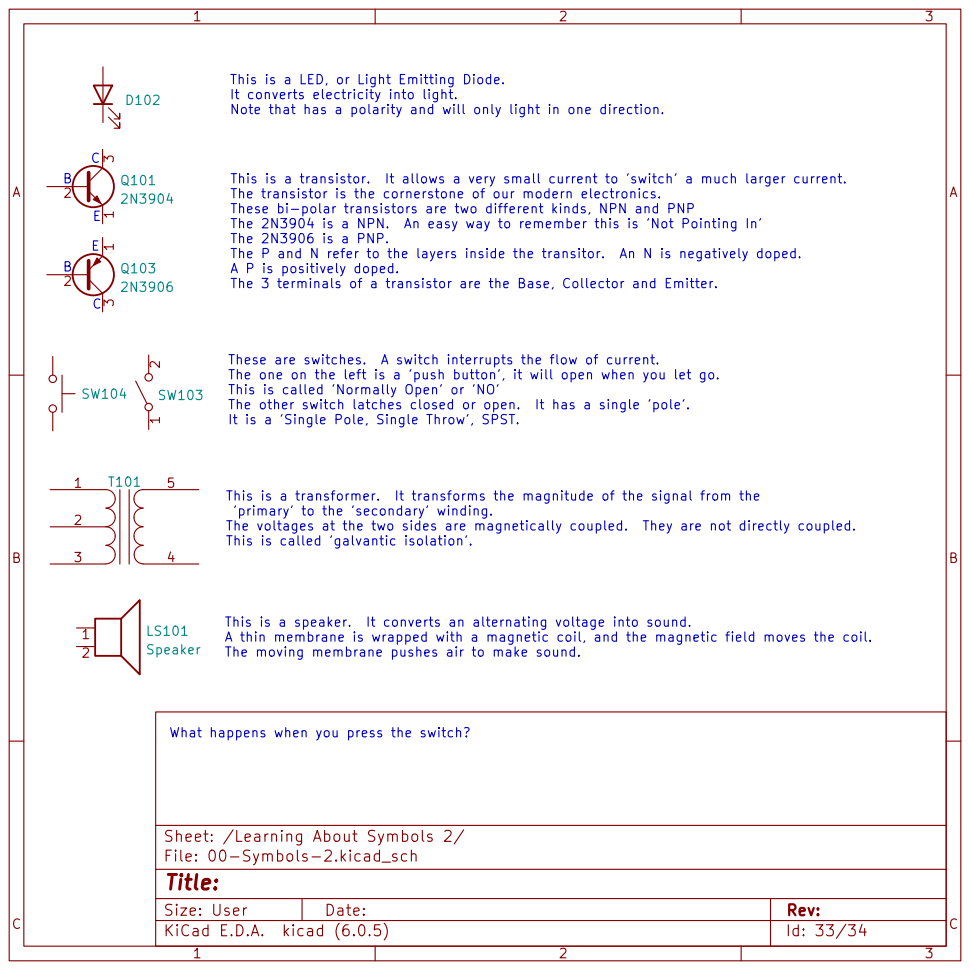
[picture p56: page 33]

This is a LED, or Light Emitting Diode.
It converts electricity into light.

This is a transistor. It allows a very small current to 'switch' a much larger current. The transistor is the cornerstone of our modern electronics. These bi-polar transistors are two different kinds, NPN and PNP

The 2N3904 is a NPN. An easy way to remember this is 'Not Pointing In' The 2N3906 is a PNP. The P and N refer to the layers inside the transitor. An N is negatively doped.

A P is positively doped. The 3 terminals of a transistor are the Base, Collector and Emitter. This is a transformer. It transforms the magnitude of the signal from the

These are switches. A switch interrupts the flow of current.
The one on the left is a 'push button', it will open when you let go.
This is called 'Normally Open' or 'NO'
The other switch latches closed or open. It has a single 'pole'.
It is a 'Single Pole, Single Throw', SPST.

'primary' to the 'secondary' winding.
The voltages at the two sides are magnetically coupled. They are not directly coupled.
This is called 'galvantic isolation'.

This is a speaker. It converts an alternating voltage into sound.
A thin membrane is wrapped with a magnetic coil, and the magnetic field moves the coil.
The moving membrane pushes air to make sound.

What happens when you press the switch?

Sheet: /Learning About Symbols 2/
File: 00-Symbols-2.kicad_sch
Id: 33/34 Title:

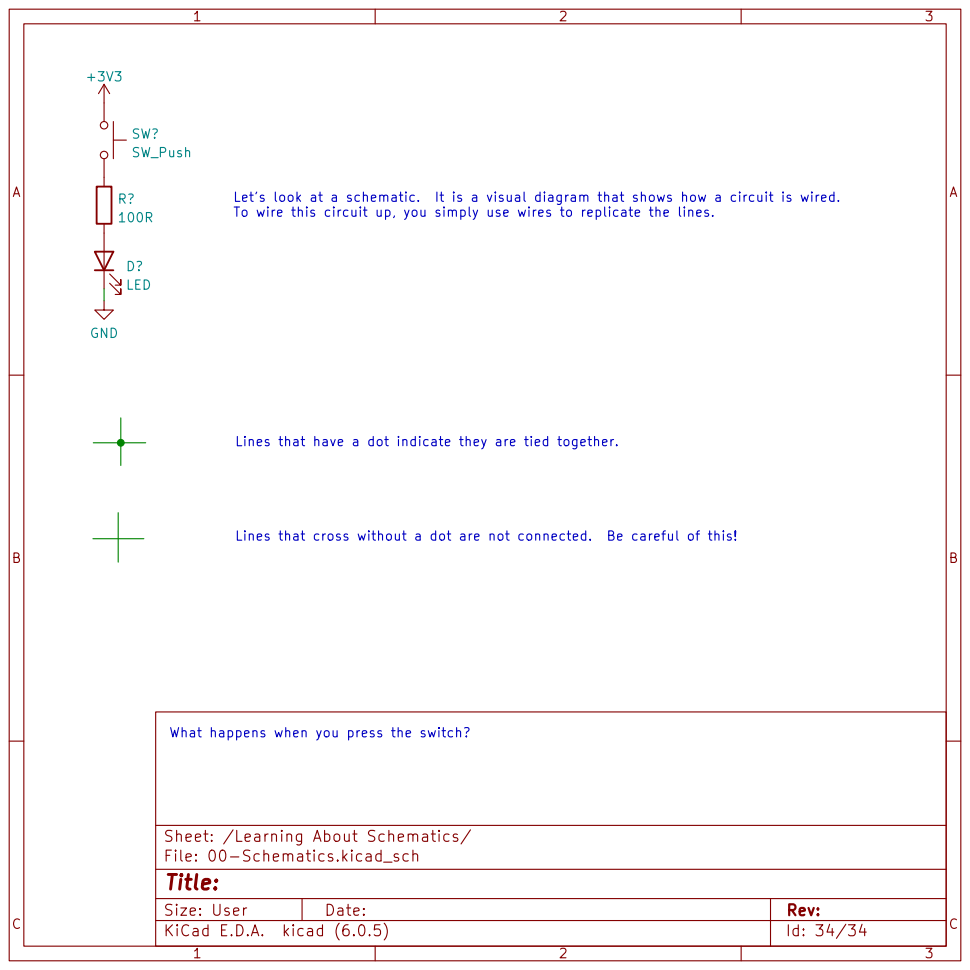
[picture p57: page 34]

Let's look at a schematic. It is a visual diagram that shows how a circuit is wired.
To wire this circuit up, you simply use wires to replicate the lines. Lines that cross without a dot are not connected. Be careful of this!

Lines that have a dot indicate they are tied together.

Sheet: /Learning About Schematics/
File: 00-Schematics.kicad_sch
Id: 34/34 Title:
