dczia/thirtyinone/Software/thirtyinone/drv_ssd1306.c

/*********************************************************************

 This was ported from the Adafruit SSD1306 library by ElectronutLabs
 for Bluey, and is licensed under the BSD 3-Clause license


 It was further ported to support the DCZia badge by @hamster

*********************************************************************/

#include <stdlib.h>
#include <string.h>
#include <atmel_start.h>

#include "drv_ssd1306.h"

struct io_descriptor *I2C_0_io;

static int8_t _i2caddr, _vccstate;

SSD1306_ROTATION _rotation;

static uint8_t LCD_Buffer[SSD1306_LCDHEIGHT * SSD1306_LCDWIDTH / 8] = { 0 };

#define ssd1306_swap(a, b) { int16_t t = a; a = b; b = t; }

static int SSD1306_width(){
    return SSD1306_LCDWIDTH;
}
static int SSD1306_height(){
    return SSD1306_LCDHEIGHT;
}
static SSD1306_ROTATION SSD1306_getRotation(){
    return _rotation;
}

// the most basic function, set a single pixel
void SSD1306_drawPixel(int16_t x, int16_t y, SSD1306_COLOR color) {
  if ((x < 0) || (x >= SSD1306_width()) || (y < 0) || (y >= SSD1306_height()))
    return;

  // check rotation, move pixel around if necessary
  switch (SSD1306_getRotation()) {
      case ROTATION_0:
          break;
      case ROTATION_90:
        ssd1306_swap(x, y);
        x = SSD1306_LCDWIDTH - x - 1;
        break;
      case ROTATION_180:
        x = SSD1306_LCDWIDTH - x - 1;
        y = SSD1306_LCDHEIGHT - y - 1;
        break;
      case ROTATION_270:
        ssd1306_swap(x, y);
        y = SSD1306_LCDHEIGHT - y - 1;
        break;
  }

  // x is which column
    int index = x+ (y/8)*SSD1306_LCDWIDTH;
    //printf("index = %d\n", index);

    switch (color){
      case COLOR_WHITE:
          LCD_Buffer[index] |=  (1 << (y&7));
          break;
      case COLOR_BLACK:
          LCD_Buffer[index] &= ~(1 << (y&7));
          break;
      case COLOR_INVERSE:
          LCD_Buffer[index] ^=  (1 << (y&7));
          break;
    }

}


void SSD1306_begin(uint8_t vccstate, uint8_t i2caddr, bool reset) {
  _vccstate = vccstate;
  _i2caddr = i2caddr;
  _rotation = ROTATION_0;
  
  i2c_m_sync_get_io_descriptor(&I2C_0, &I2C_0_io);
  i2c_m_sync_set_slaveaddr(&I2C_0, SSD1306_I2C_ADDRESS, I2C_M_SEVEN);
  i2c_m_sync_enable(&I2C_0);

  // Init sequence
  SSD1306_command(SSD1306_DISPLAYOFF);                    // 0xAE
  SSD1306_command(SSD1306_SETDISPLAYCLOCKDIV);            // 0xD5
  SSD1306_command(0x80);                                  // the suggested ratio 0x80

  SSD1306_command(SSD1306_SETMULTIPLEX);                  // 0xA8
  SSD1306_command(SSD1306_LCDHEIGHT - 1);

  SSD1306_command(SSD1306_SETDISPLAYOFFSET);              // 0xD3
  SSD1306_command(0x0);                                   // no offset
  SSD1306_command(SSD1306_SETSTARTLINE | 0x0);            // line #0
  SSD1306_command(SSD1306_CHARGEPUMP);                    // 0x8D
  if (vccstate == SSD1306_EXTERNALVCC){
      SSD1306_command(0x10);
  }
  else{
      SSD1306_command(0x14);
  }
  SSD1306_command(SSD1306_MEMORYMODE);                    // 0x20
  SSD1306_command(0x00);                                  // 0x0 act like ks0108
  SSD1306_command(SSD1306_SEGREMAP | 0x1);
  SSD1306_command(SSD1306_COMSCANDEC);

 #if defined SSD1306_128_32
  SSD1306_command(SSD1306_SETCOMPINS);                    // 0xDA
  SSD1306_command(0x02);
  SSD1306_command(SSD1306_SETCONTRAST);                   // 0x81
  SSD1306_command(0x8F);

#elif defined SSD1306_128_64
  SSD1306_command(SSD1306_SETCOMPINS);                    // 0xDA
  SSD1306_command(0x12);
  SSD1306_command(SSD1306_SETCONTRAST);                   // 0x81
  if (vccstate == SSD1306_EXTERNALVCC)
    { SSD1306_command(0x9F); }
  else
    { SSD1306_command(0xCF); }

#elif defined SSD1306_96_16
  SSD1306_command(SSD1306_SETCOMPINS);                    // 0xDA
  SSD1306_command(0x2);   //ada x12
  SSD1306_command(SSD1306_SETCONTRAST);                   // 0x81
  if (vccstate == SSD1306_EXTERNALVCC)
    { SSD1306_command(0x10); }
  else
    { SSD1306_command(0xAF); }

#endif

  SSD1306_command(SSD1306_SETPRECHARGE);                  // 0xd9
  if (vccstate == SSD1306_EXTERNALVCC)
    { SSD1306_command(0x22); }
  else
    { SSD1306_command(0xF1); }
  SSD1306_command(SSD1306_SETVCOMDETECT);                 // 0xDB
  SSD1306_command(0x40);
  SSD1306_command(SSD1306_DISPLAYALLON_RESUME);           // 0xA4
  SSD1306_command(SSD1306_NORMALDISPLAY);                 // 0xA6

  SSD1306_command(SSD1306_DEACTIVATE_SCROLL);

  SSD1306_command(SSD1306_DISPLAYON);//--turn on oled panel
}


void SSD1306_invertDisplay(uint8_t i) {
  if (i) {
    SSD1306_command(SSD1306_INVERTDISPLAY);
  } else {
    SSD1306_command(SSD1306_NORMALDISPLAY);
  }
}

void SSD1306_setRotation(SSD1306_ROTATION rotation){
    _rotation = rotation;
}

void SSD1306_command(uint8_t c){
	uint8_t data[2] = { 0x00, 0x00 };
	data[1] = c;
	io_write(I2C_0_io, data, 2);
}

// startscrollright
// Activate a right handed scroll for rows start through stop
// Hint, the display is 16 rows tall. To scroll the whole display, run:
// display.scrollright(0x00, 0x0F)
void SSD1306_startscrollright(uint8_t start, uint8_t stop){
  SSD1306_command(SSD1306_RIGHT_HORIZONTAL_SCROLL);
  SSD1306_command(0X00);
  SSD1306_command(start);
  SSD1306_command(0X00);
  SSD1306_command(stop);
  SSD1306_command(0X00);
  SSD1306_command(0XFF);
  SSD1306_command(SSD1306_ACTIVATE_SCROLL);
}

// startscrollleft
// Activate a right handed scroll for rows start through stop
// Hint, the display is 16 rows tall. To scroll the whole display, run:
// display.scrollright(0x00, 0x0F)
void SSD1306_startscrollleft(uint8_t start, uint8_t stop){
  SSD1306_command(SSD1306_LEFT_HORIZONTAL_SCROLL);
  SSD1306_command(0X00);
  SSD1306_command(start);
  SSD1306_command(0X00);
  SSD1306_command(stop);
  SSD1306_command(0X00);
  SSD1306_command(0XFF);
  SSD1306_command(SSD1306_ACTIVATE_SCROLL);
}

// startscrolldiagright
// Activate a diagonal scroll for rows start through stop
// Hint, the display is 16 rows tall. To scroll the whole display, run:
// display.scrollright(0x00, 0x0F)
void SSD1306_startscrolldiagright(uint8_t start, uint8_t stop){
  SSD1306_command(SSD1306_SET_VERTICAL_SCROLL_AREA);
  SSD1306_command(0X00);
  SSD1306_command(SSD1306_LCDHEIGHT);
  SSD1306_command(SSD1306_VERTICAL_AND_RIGHT_HORIZONTAL_SCROLL);
  SSD1306_command(0X00);
  SSD1306_command(start);
  SSD1306_command(0X00);
  SSD1306_command(stop);
  SSD1306_command(0X01);
  SSD1306_command(SSD1306_ACTIVATE_SCROLL);
}

// startscrolldiagleft
// Activate a diagonal scroll for rows start through stop
// Hint, the display is 16 rows tall. To scroll the whole display, run:
// display.scrollright(0x00, 0x0F)
void SSD1306_startscrolldiagleft(uint8_t start, uint8_t stop){
  SSD1306_command(SSD1306_SET_VERTICAL_SCROLL_AREA);
  SSD1306_command(0X00);
  SSD1306_command(SSD1306_LCDHEIGHT);
  SSD1306_command(SSD1306_VERTICAL_AND_LEFT_HORIZONTAL_SCROLL);
  SSD1306_command(0X00);
  SSD1306_command(start);
  SSD1306_command(0X00);
  SSD1306_command(stop);
  SSD1306_command(0X01);
  SSD1306_command(SSD1306_ACTIVATE_SCROLL);
}

void SSD1306_stopscroll(void){
  SSD1306_command(SSD1306_DEACTIVATE_SCROLL);
}

// Dim the display
// dim = true: display is dimmed
// dim = false: display is normal
void SSD1306_dim(bool dim) {
  uint8_t contrast;

  if (dim) {
    contrast = 0; // Dimmed display
  } else {
    if (_vccstate == SSD1306_EXTERNALVCC) {
      contrast = 0x9F;
    } else {
      contrast = 0xCF;
    }
  }
  // the range of contrast to too small to be really useful
  // it is useful to dim the display
  SSD1306_command(SSD1306_SETCONTRAST);
  SSD1306_command(contrast);
}

void SSD1306_display(void){
  SSD1306_command(SSD1306_COLUMNADDR);
  SSD1306_command(0);   // Column start address (0 = reset)
  SSD1306_command(SSD1306_LCDWIDTH-1); // Column end address (127 = reset)

  SSD1306_command(SSD1306_PAGEADDR);
  SSD1306_command(0); // Page start address (0 = reset)
  #if SSD1306_LCDHEIGHT == 64
    SSD1306_command(7); // Page end address
  #endif
  #if SSD1306_LCDHEIGHT == 32
    SSD1306_command(3); // Page end address
  #endif
  #if SSD1306_LCDHEIGHT == 16
    SSD1306_command(1); // Page end address
  #endif

    // I2C
    for (uint16_t i=0; i<(SSD1306_LCDWIDTH*SSD1306_LCDHEIGHT/8); i++) {
      uint8_t tmpBuf[17];
      tmpBuf[0] = SSD1306_SETSTARTLINE;
      // data
      for (uint8_t j = 0; j < 16; j++) {
        tmpBuf[j+1] = LCD_Buffer[i];
        i++;
      }
      i--;

		io_write(I2C_0_io, tmpBuf, sizeof(tmpBuf));
    }

}

// clear everything
void SSD1306_clearDisplay(void) {
  memset(LCD_Buffer, 0, (SSD1306_LCDWIDTH*SSD1306_LCDHEIGHT/8));
}


void SSD1306_drawFastHLine(int16_t x, int16_t y, int16_t w, SSD1306_COLOR color) {
  bool bSwap = false;
  switch(SSD1306_getRotation()) {
    case ROTATION_0:
      // 0 degree rotation, do nothing
      break;
    case ROTATION_90:
      // 90 degree rotation, swap x & y for rotation, then invert x
      bSwap = true;
      ssd1306_swap(x, y);
      x = SSD1306_LCDWIDTH - x - 1;
      break;
    case ROTATION_180:
      // 180 degree rotation, invert x and y - then shift y around for height.
      x = SSD1306_LCDWIDTH - x - 1;
      y = SSD1306_LCDHEIGHT - y - 1;
      x -= (w-1);
      break;
    case ROTATION_270:
      // 270 degree rotation, swap x & y for rotation, then invert y  and adjust y for w (not to become h)
      bSwap = true;
      ssd1306_swap(x, y);
      y = SSD1306_LCDHEIGHT - y - 1;
      y -= (w-1);
      break;
  }

  if(bSwap) {
    SSD1306_drawFastVLineInternal(x, y, w, color);
  } else {
    SSD1306_drawFastHLineInternal(x, y, w, color);
  }
}

void SSD1306_drawFastHLineInternal(int16_t x, int16_t y, int16_t w, SSD1306_COLOR color) {
  // Do bounds/limit checks
  if(y < 0 || y >= SSD1306_LCDHEIGHT) { return; }

  // make sure we don't try to draw below 0
  if(x < 0) {
    w += x;
    x = 0;
  }

  // make sure we don't go off the edge of the display
  if( (x + w) > SSD1306_LCDWIDTH) {
    w = (SSD1306_LCDWIDTH - x);
  }

  // if our width is now negative, punt
  if(w <= 0) { return; }

  // set up the pointer for  movement through the LCD_Buffer
  register uint8_t *pBuf = LCD_Buffer;
  // adjust the LCD_Buffer pointer for the current row
  pBuf += ((y/8) * SSD1306_LCDWIDTH);
  // and offset x columns in
  pBuf += x;

  register uint8_t mask = 1 << (y&7);

  switch (color){
    case COLOR_WHITE:
        while(w--){
            *pBuf++ |= mask;
        };
        break;
    case COLOR_BLACK:
        mask = ~mask;
        while(w--){
            *pBuf++ &= mask;
        };
        break;
    case COLOR_INVERSE:
        while(w--){
            *pBuf++ ^= mask;
        };
        break;
  }
}

void SSD1306_drawFastVLine(int16_t x, int16_t y, int16_t h, SSD1306_COLOR color) {
  bool bSwap = false;
  switch(SSD1306_getRotation()) {
    case 0:
      break;
    case 1:
      // 90 degree rotation, swap x & y for rotation, then invert x and adjust x for h (now to become w)
      bSwap = true;
      ssd1306_swap(x, y);
      x = SSD1306_LCDWIDTH - x - 1;
      x -= (h-1);
      break;
    case 2:
      // 180 degree rotation, invert x and y - then shift y around for height.
      x = SSD1306_LCDWIDTH - x - 1;
      y = SSD1306_LCDHEIGHT - y - 1;
      y -= (h-1);
      break;
    case 3:
      // 270 degree rotation, swap x & y for rotation, then invert y
      bSwap = true;
      ssd1306_swap(x, y);
      y = SSD1306_LCDHEIGHT - y - 1;
      break;
  }

  if(bSwap) {
    SSD1306_drawFastHLineInternal(x, y, h, color);
  } else {
    SSD1306_drawFastVLineInternal(x, y, h, color);
  }
}


void SSD1306_drawFastVLineInternal(int16_t x, int16_t __y, int16_t __h, SSD1306_COLOR color) {

  // do nothing if we're off the left or right side of the screen
  if(x < 0 || x >= SSD1306_LCDWIDTH) { return; }

  // make sure we don't try to draw below 0
  if(__y < 0) {
    // __y is negative, this will subtract enough from __h to account for __y being 0
    __h += __y;
    __y = 0;

  }

  // make sure we don't go past the height of the display
  if( (__y + __h) > SSD1306_LCDHEIGHT) {
    __h = (SSD1306_LCDHEIGHT - __y);
  }

  // if our height is now negative, punt
  if(__h <= 0) {
    return;
  }

  // this display doesn't need ints for coordinates, use local byte registers for faster juggling
  register uint8_t y = __y;
  register uint8_t h = __h;


  // set up the pointer for fast movement through the LCD_Buffer
  register uint8_t *pBuf = LCD_Buffer;
  // adjust the LCD_Buffer pointer for the current row
  pBuf += ((y/8) * SSD1306_LCDWIDTH);
  // and offset x columns in
  pBuf += x;

  // do the first partial byte, if necessary - this requires some masking
  register uint8_t mod = (y&7);
  if(mod) {
    // mask off the high n bits we want to set
    mod = 8-mod;

    // note - lookup table results in a nearly 10% performance improvement in fill* functions
    // register uint8_t mask = ~(0xFF >> (mod));
    static uint8_t premask[8] = {0x00, 0x80, 0xC0, 0xE0, 0xF0, 0xF8, 0xFC, 0xFE };
    register uint8_t mask = premask[mod];

    // adjust the mask if we're not going to reach the end of this byte
    if( h < mod) {
      mask &= (0XFF >> (mod-h));
    }

  switch (color){
    case COLOR_WHITE:
        *pBuf |=  mask;
        break;
    case COLOR_BLACK:
        *pBuf &= ~mask;
        break;
    case COLOR_INVERSE:
        *pBuf ^=  mask;
        break;
    }

    // fast exit if we're done here!
    if(h<mod) { return; }

    h -= mod;

    pBuf += SSD1306_LCDWIDTH;
  }


  // write solid bytes while we can - effectively doing 8 rows at a time
  if(h >= 8) {
    if (color == COLOR_INVERSE)  {          // separate copy of the code so we don't impact performance of the black/white write version with an extra comparison per loop
      do  {
      *pBuf=~(*pBuf);

        // adjust the LCD_Buffer forward 8 rows worth of data
        pBuf += SSD1306_LCDWIDTH;

        // adjust h & y (there's got to be a faster way for me to do this, but this should still help a fair bit for now)
        h -= 8;
      } while(h >= 8);
      }
    else {
      // store a local value to work with
      register uint8_t val = (color == COLOR_WHITE) ? 255 : 0;

      do  {
        // write our value in
      *pBuf = val;

        // adjust the LCD_Buffer forward 8 rows worth of data
        pBuf += SSD1306_LCDWIDTH;

        // adjust h & y (there's got to be a faster way for me to do this, but this should still help a fair bit for now)
        h -= 8;
      } while(h >= 8);
      }
    }

  // now do the final partial byte, if necessary
  if(h) {
    mod = h & 7;
    // this time we want to mask the low bits of the byte, vs the high bits we did above
    // register uint8_t mask = (1 << mod) - 1;
    // note - lookup table results in a nearly 10% performance improvement in fill* functions
    static uint8_t postmask[8] = {0x00, 0x01, 0x03, 0x07, 0x0F, 0x1F, 0x3F, 0x7F };
    register uint8_t mask = postmask[mod];
    switch (color){
      case COLOR_WHITE:
          *pBuf |=  mask;
          break;
      case COLOR_BLACK:
          *pBuf &= ~mask;
          break;
      case COLOR_INVERSE:
          *pBuf ^=  mask;
          break;
    }
  }
}
